Dholydai/writerz-with-an-attitude/KeycapSubs/Keycaps-for-single-hand-comp.jpg

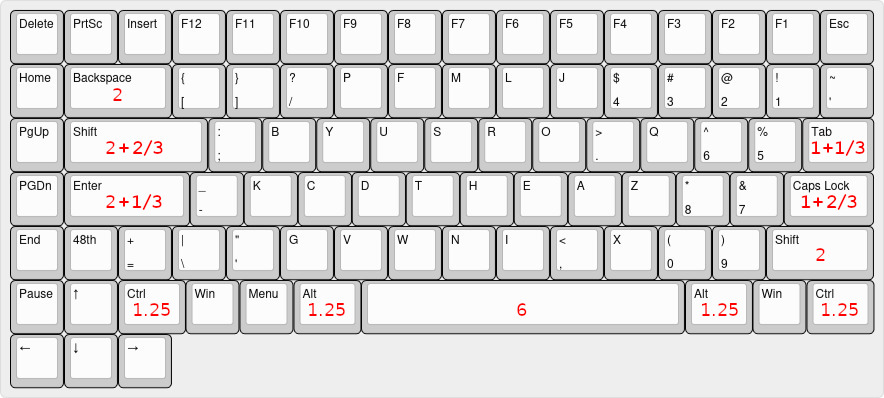
KeycapSubs/Keycaps-for-single-hand-comp.jpg
