Dholydai/writerz-with-an-attitude/KeycapSubs/Keycaps-for-two-hand-comp.png

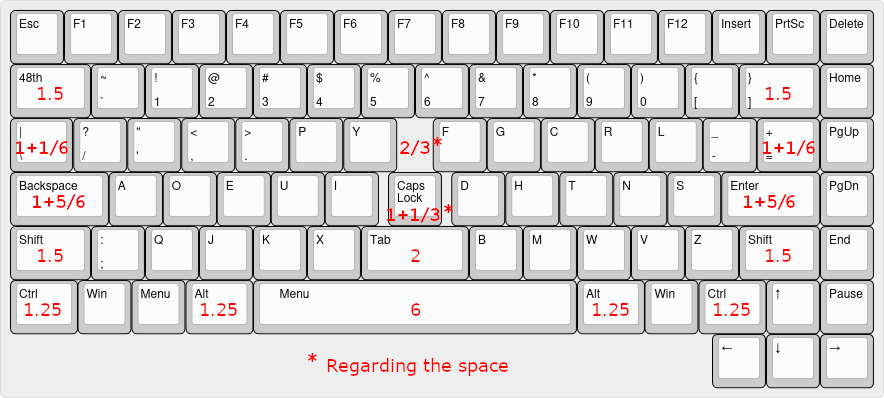
KeycapSubs/Keycaps-for-two-hand-comp.png
