Dholydai/writerz-with-an-attitude/KeycapSubs/Single-hand-keycap-subs.png

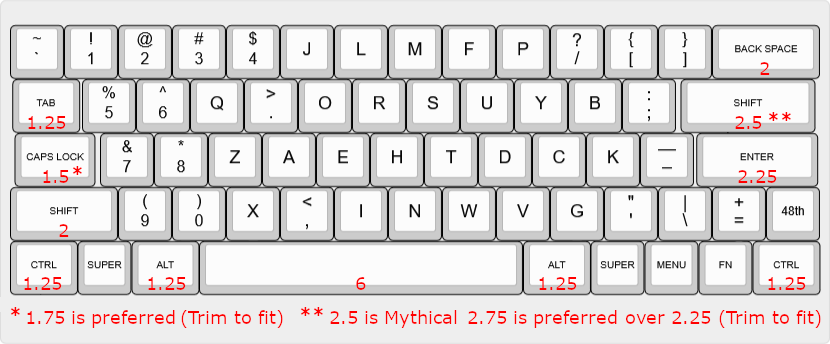
KeycapSubs/Single-hand-keycap-subs.png
