Dholydai/writerz-with-an-attitude/KeycapSubs/Two-hand-keycap-subs.png

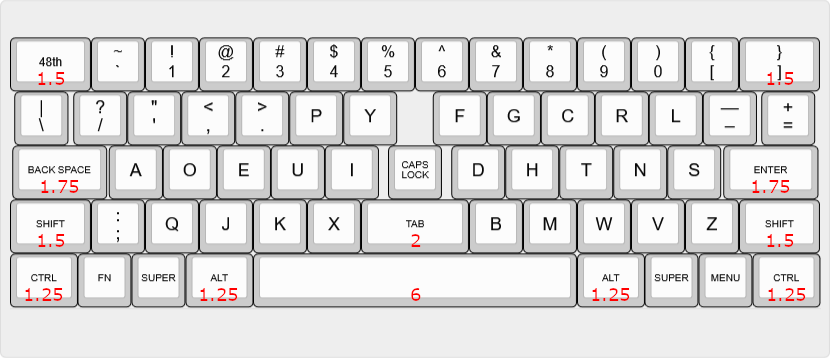
KeycapSubs/Two-hand-keycap-subs.png
