Dholydai/writerz-with-an-attitude/Layout/Dhlyd2Hnd60Lft.png

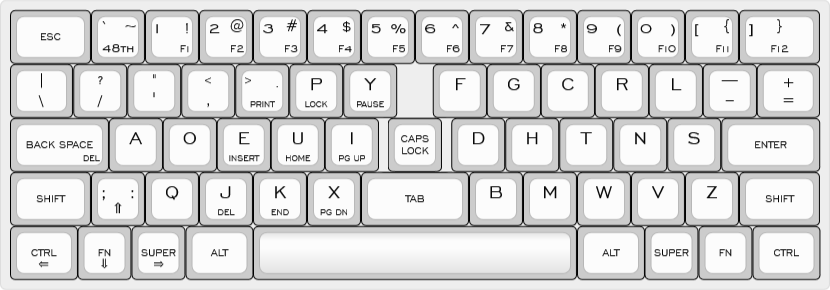
Layout/Dhlyd2Hnd60Lft.png
