Dholydai/writerz-with-an-attitude/Layout/Dhlyd2Hnd60Rgt.png

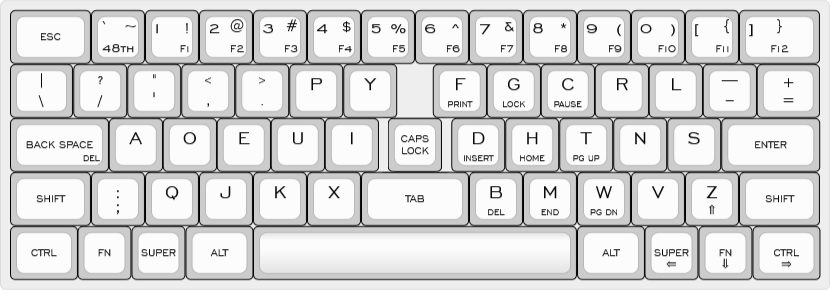
Layout/Dhlyd2Hnd60Rgt.png
