Dholydai/writerz-with-an-attitude/Layout/Dhlyd2HndCmp.png

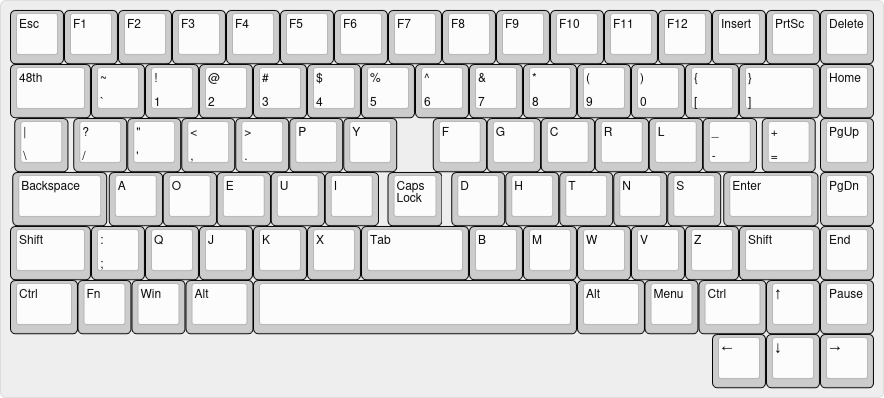
Layout/Dhlyd2HndCmp.png
