Dholydai/writerz-with-an-attitude/Layout/Dhlyd2HndMax.png

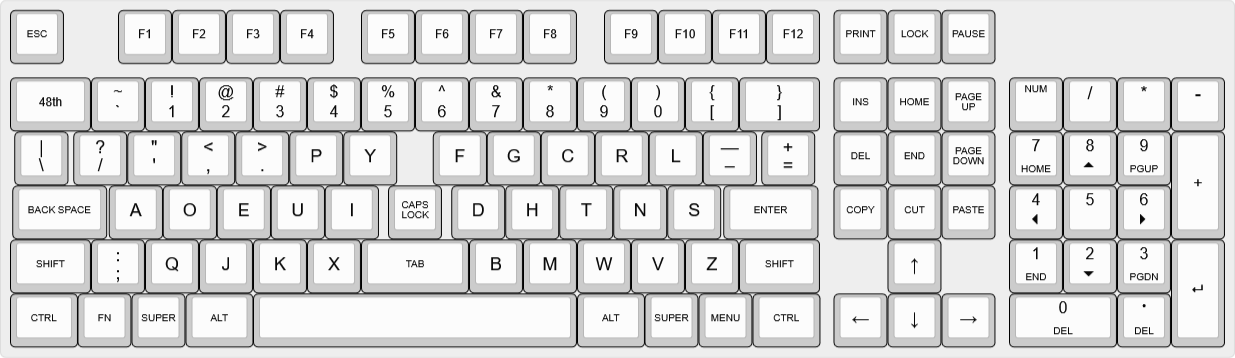
Layout/Dhlyd2HndMax.png
