Dholydai/writerz-with-an-attitude/Layout/DhlydLeftComp.png

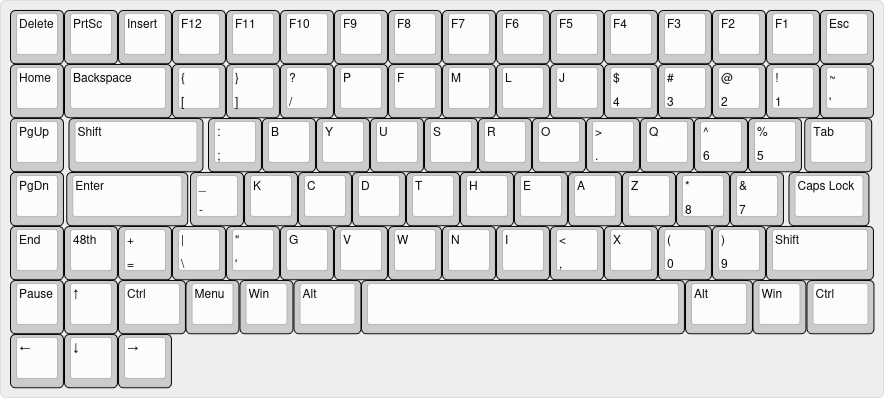
Layout/DhlydLeftComp.png
