Dholydai/writerz-with-an-attitude/Layout/DhlydRightComp.png

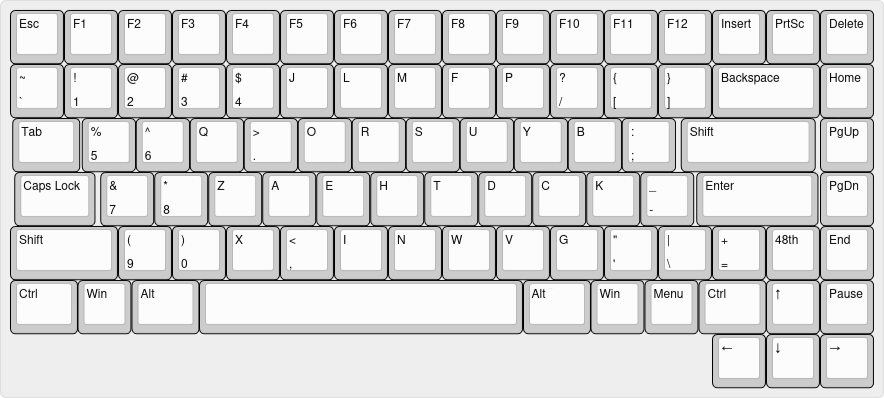
Layout/DhlydRightComp.png
