Dholydai/writerz-with-an-attitude/Matrix/Dhlyd2HndCmp.png

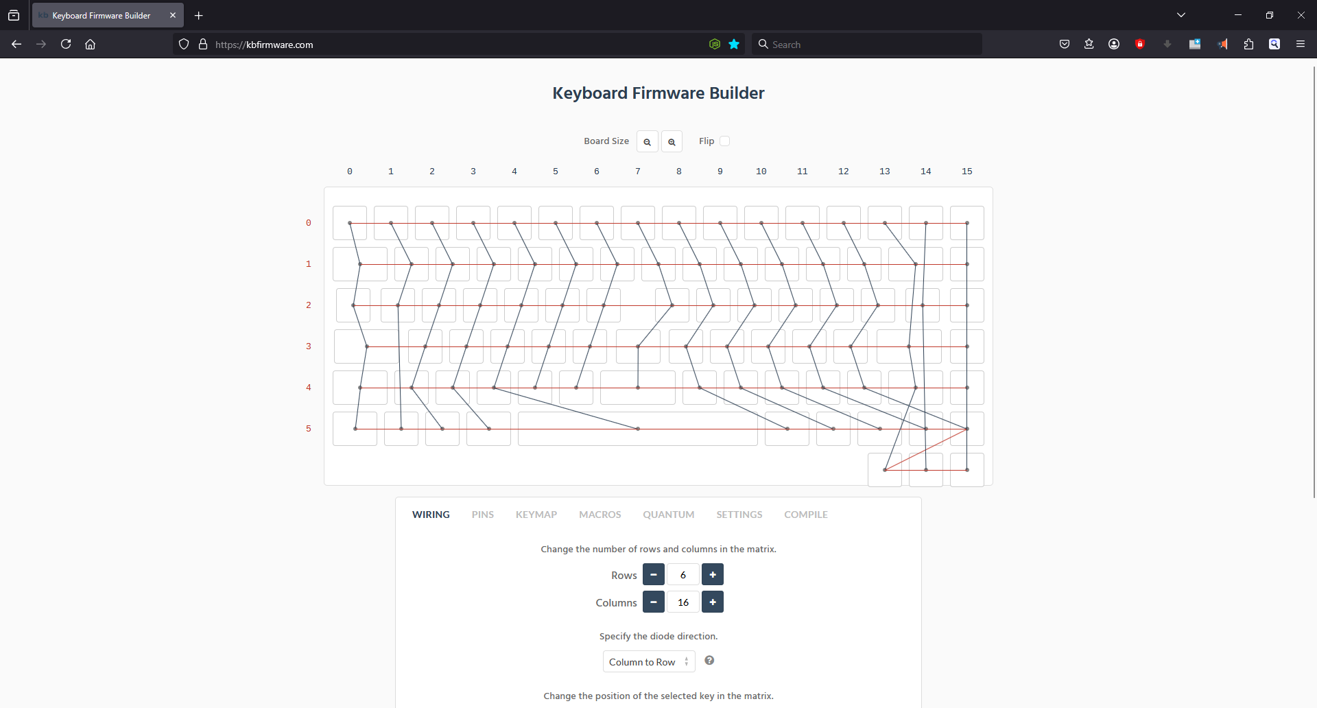
Matrix/Dhlyd2HndCmp.png
