Dholydai/writerz-with-an-attitude/Matrix/Dhlyd2HndMax.png

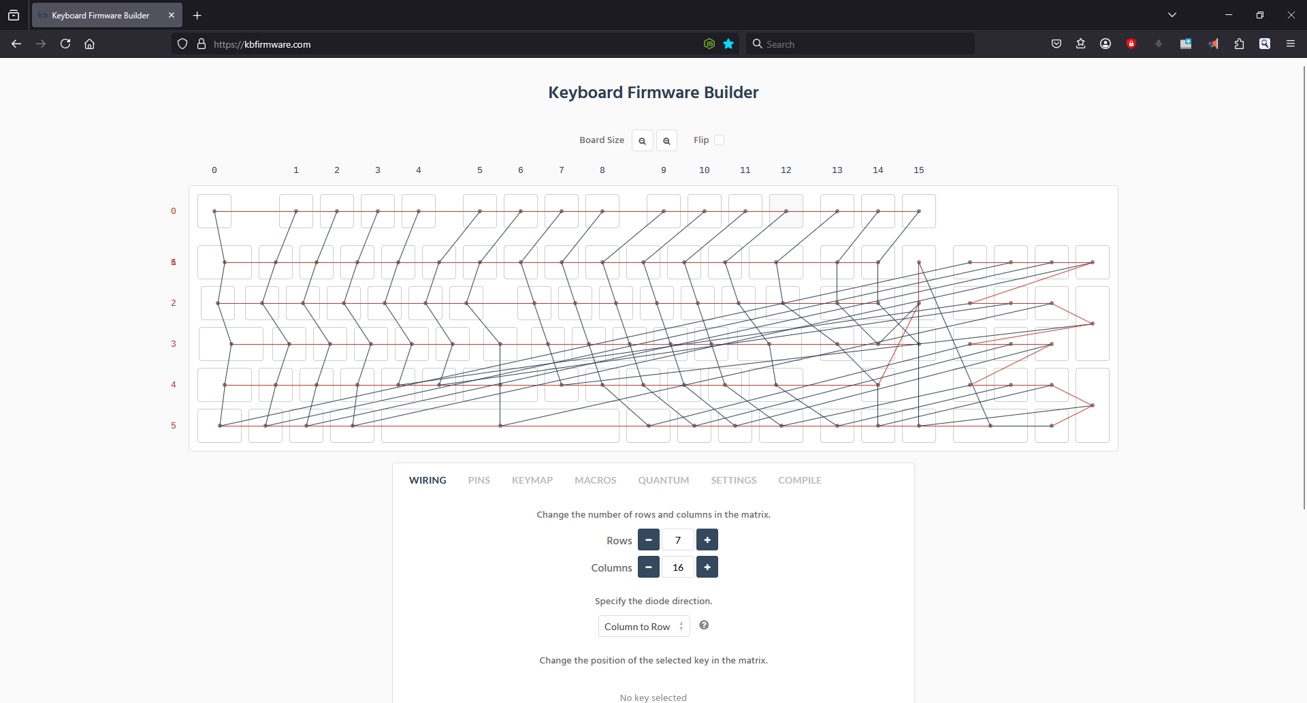
Matrix/Dhlyd2HndMax.png
