Dholydai/writerz-with-an-attitude/Matrix/DhlydLeftCmp.png

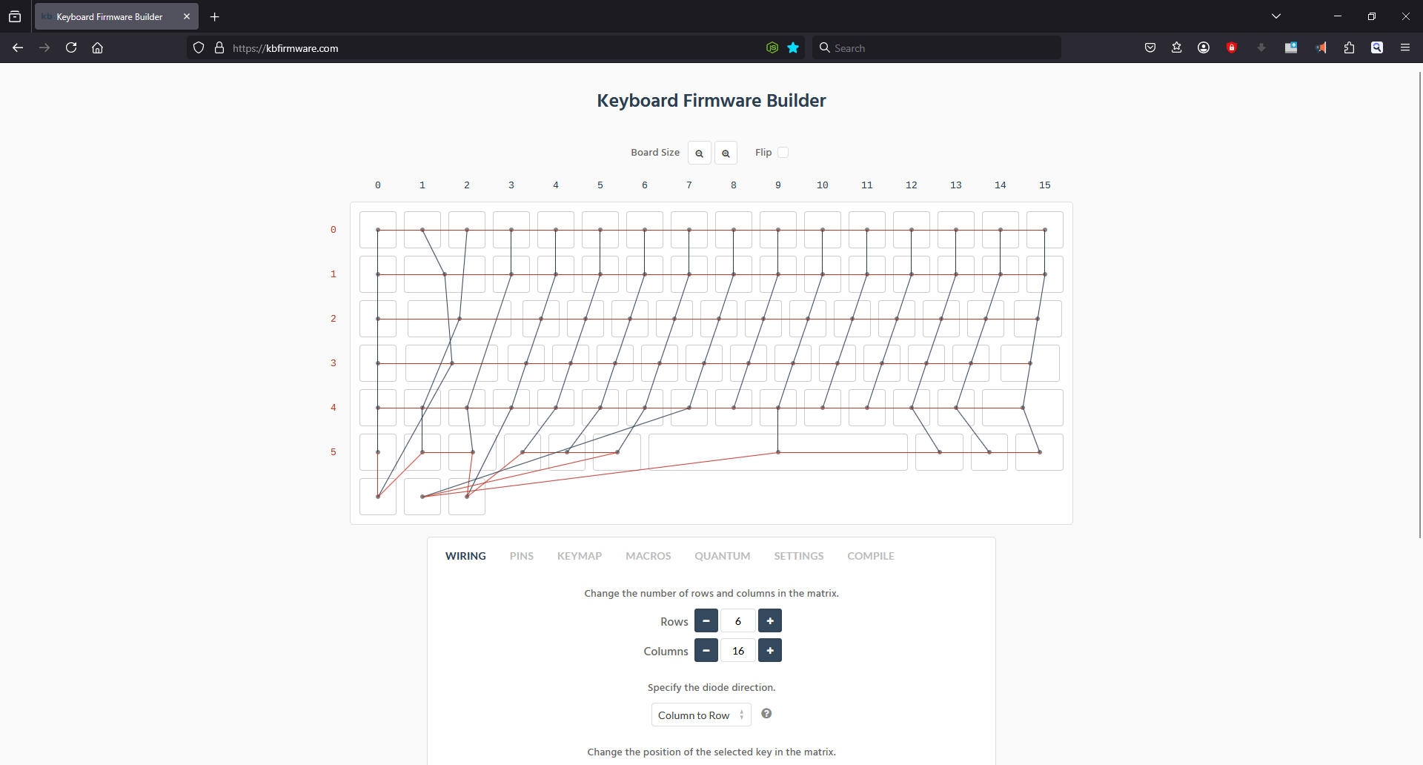
Matrix/DhlydLeftCmp.png
