Dholydai/writerz-with-an-attitude/Nuevo Universal/Brazil/BlkQX1-Brazil.png

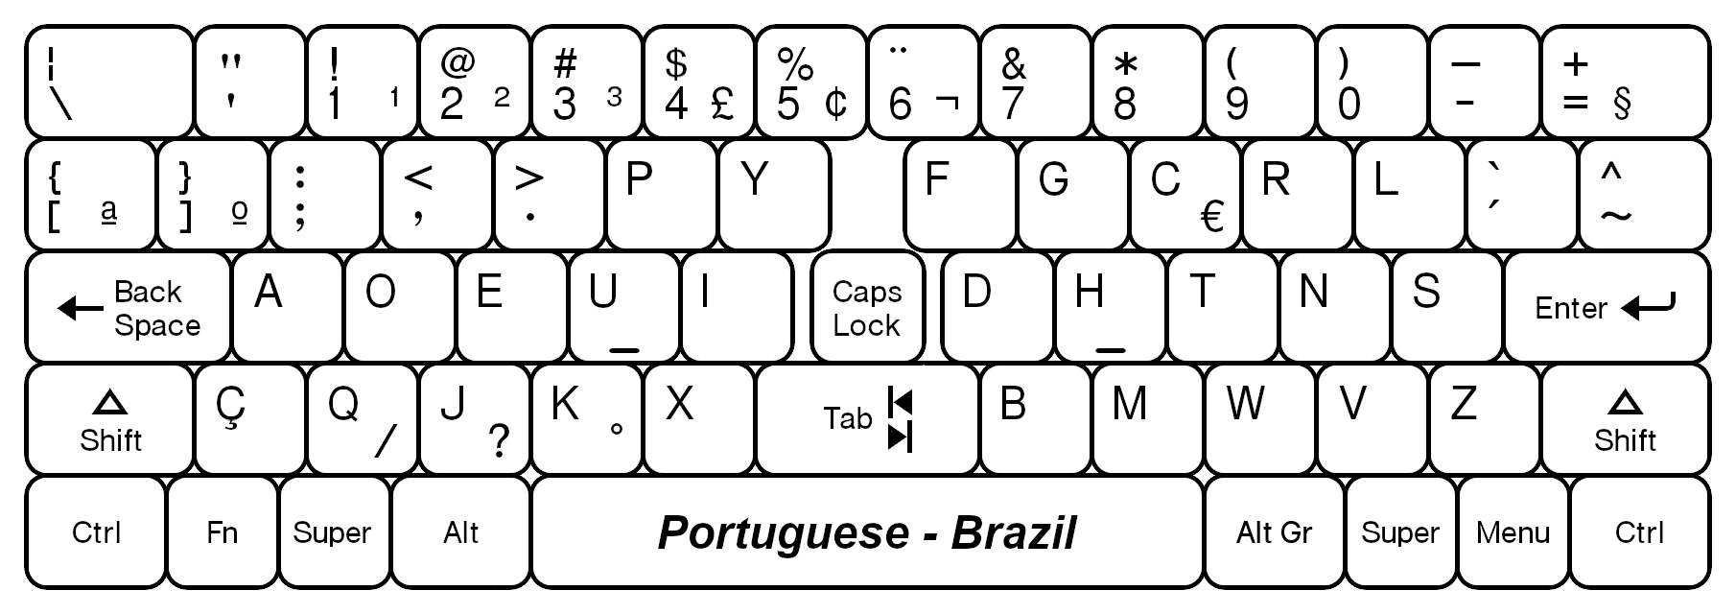
Nuevo Universal/Brazil/BlkQX1-Brazil.png
