Dholydai/writerz-with-an-attitude/Nuevo Universal/Czechia/BlkQX1-Czech.png

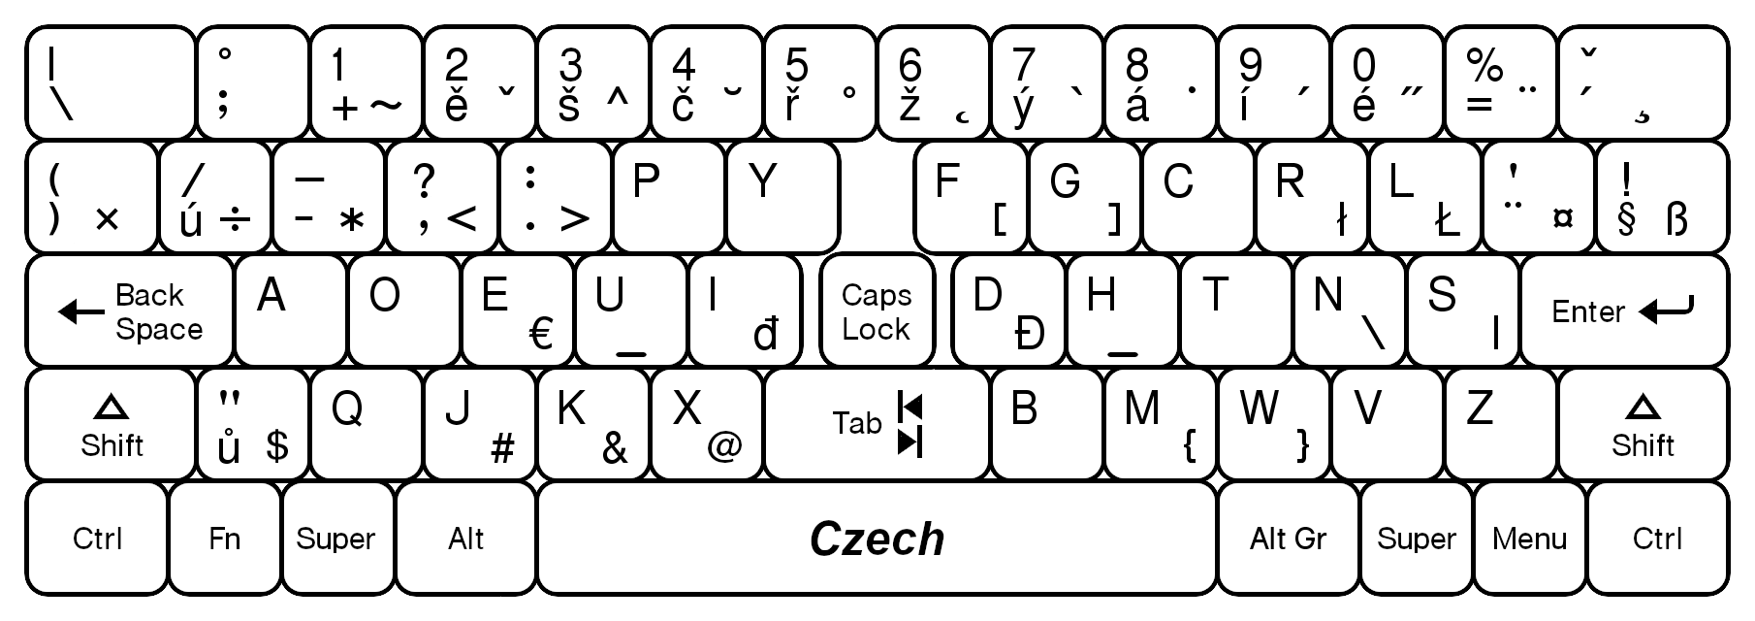
Nuevo Universal/Czechia/BlkQX1-Czech.png
