Dholydai/writerz-with-an-attitude/Nuevo Universal/Spain/BlkQX1-Spanish.png

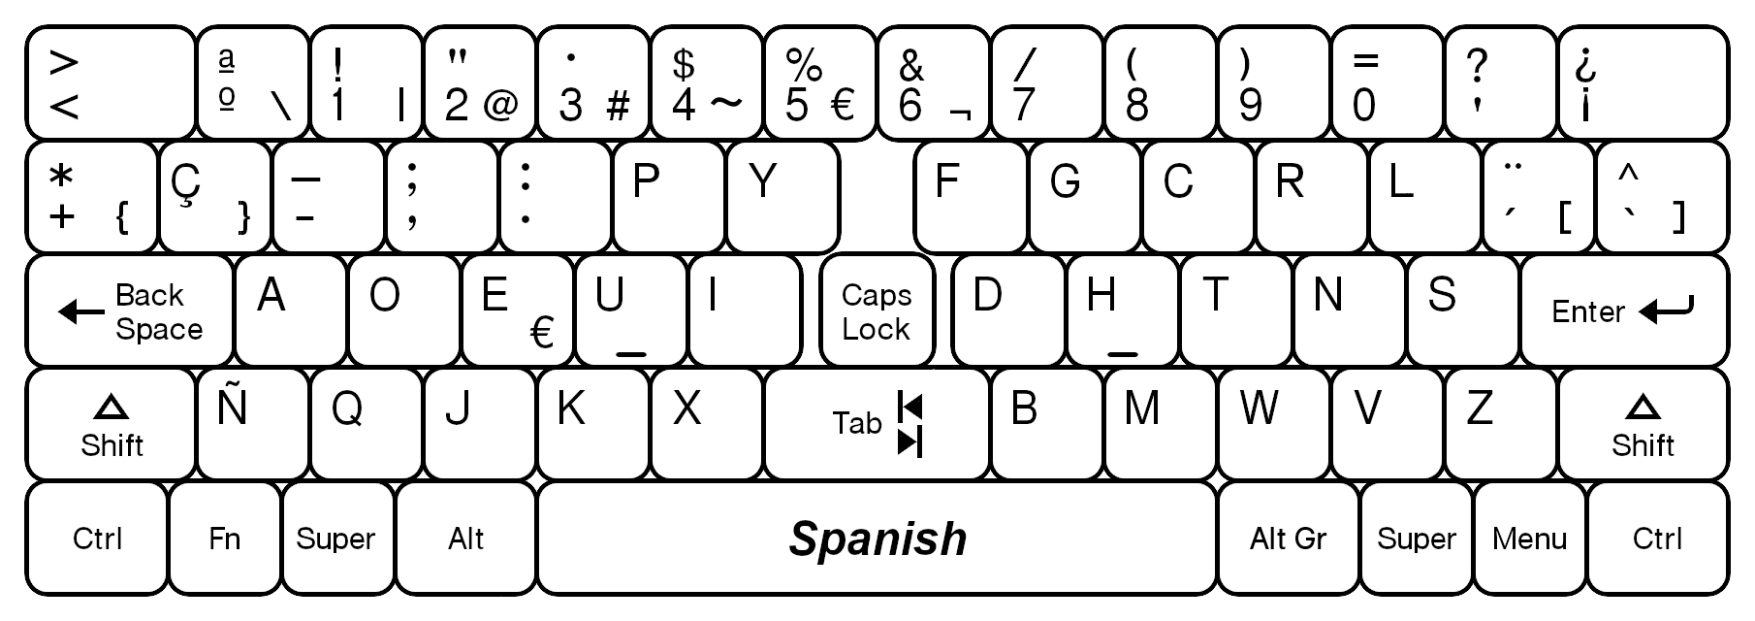
Nuevo Universal/Spain/BlkQX1-Spanish.png
