Dholydai/writerz-with-an-attitude/Dhlyd2HandMaximus/Case2HndMaximus/Stl/Max2HndBtmRgt.stl

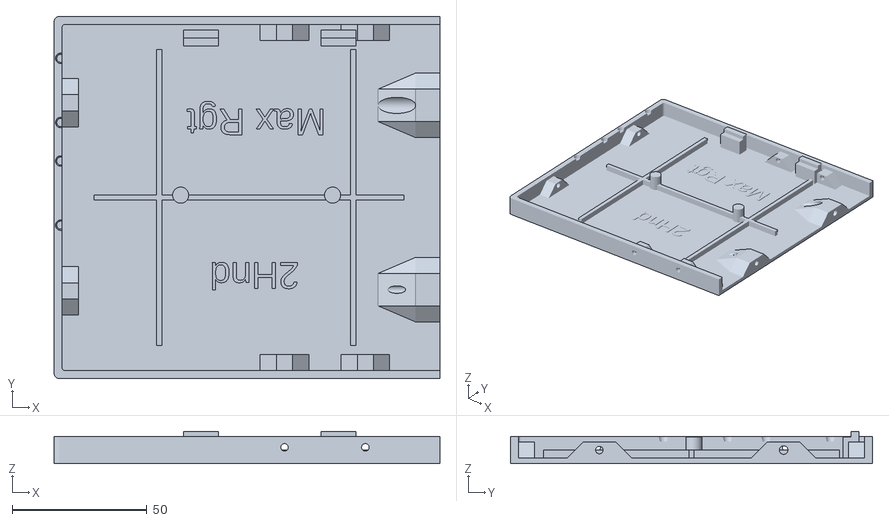
[picture p41: CAD file, 2026-07-24]
Dhlyd2HandMaximus/Case2HndMaximus/Stl/Max2HndBtmRgt.stl
143.2 x 134.3 x 11.9
