Dholydai/writerz-with-an-attitude/Dhlyd2HandCompact/Case2HndComp/Stl/Comp2HndTopRgt.stl

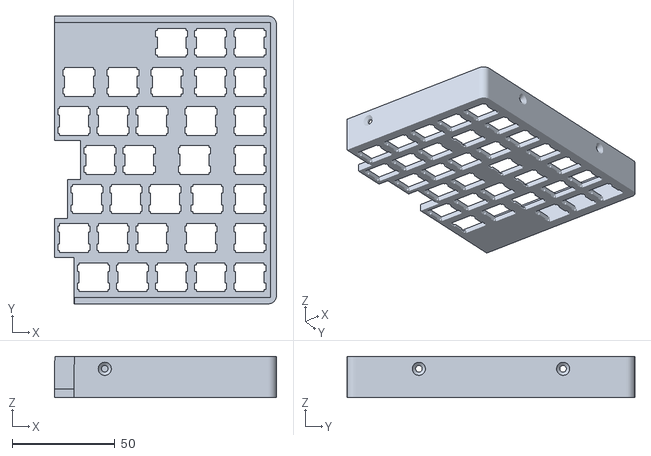
[picture p42: CAD file, 2026-07-24]
Dhlyd2HandCompact/Case2HndComp/Stl/Comp2HndTopRgt.stl
108.3 x 140.4 x 20.0
