Dholydai/writerz-with-an-attitude/DhlydRightCompact/CaseRightHndComp/Stl/CompRightTopRgt.stl

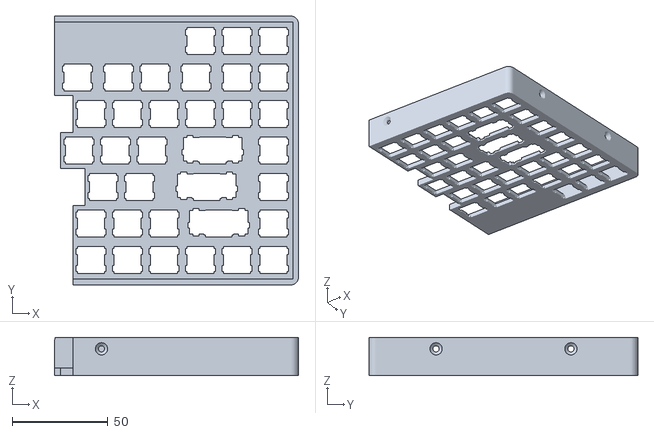
[picture p43: CAD file, 2026-07-24]
DhlydRightCompact/CaseRightHndComp/Stl/CompRightTopRgt.stl
127.3 x 140.4 x 20.0
