Dholydai/writerz-with-an-attitude/Dhlyd2Hand60Percent/Case2Hnd60Per/Stl/SixtyTopLft.stl

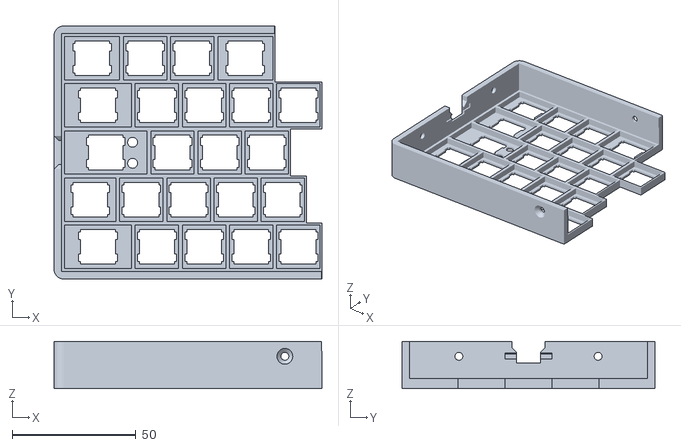
[picture p44: CAD file, 2026-07-24]
Dhlyd2Hand60Percent/Case2Hnd60Per/Stl/SixtyTopLft.stl
108.3 x 102.2 x 19.0
