Dholydai/writerz-with-an-attitude/Dhlyd2HandMaximus/Case2HndMaximus/Stl/Max2HndTopRgt.stl

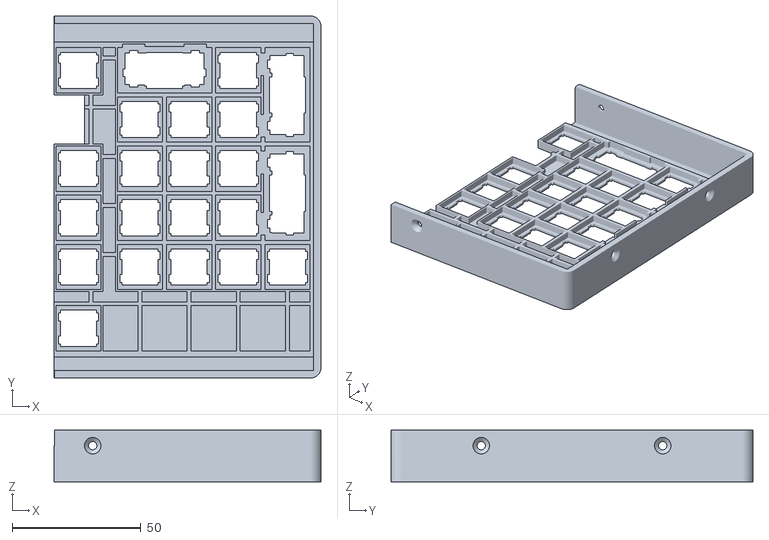
[picture p45: CAD file, 2026-07-24]
Dhlyd2HandMaximus/Case2HndMaximus/Stl/Max2HndTopRgt.stl
103.5 x 140.4 x 20.0
