Dholydai/writerz-with-an-attitude/Dhlyd2HandMaximus/Case2HndMaximus/Stl/Max2HndBtmMid.stl

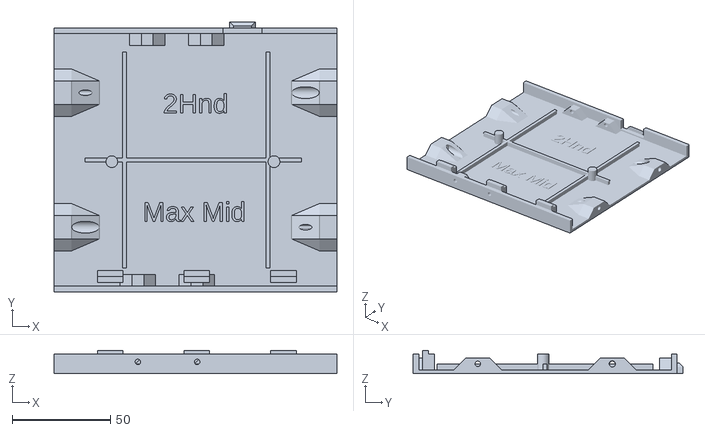
[picture p46: CAD file, 2026-07-24]
Dhlyd2HandMaximus/Case2HndMaximus/Stl/Max2HndBtmMid.stl
143.8 x 137.3 x 11.9
