Dholydai/writerz-with-an-attitude/Dhlyd2HandMaximus/Case2HndMaximus/Stl/Max2HndTopLft.stl

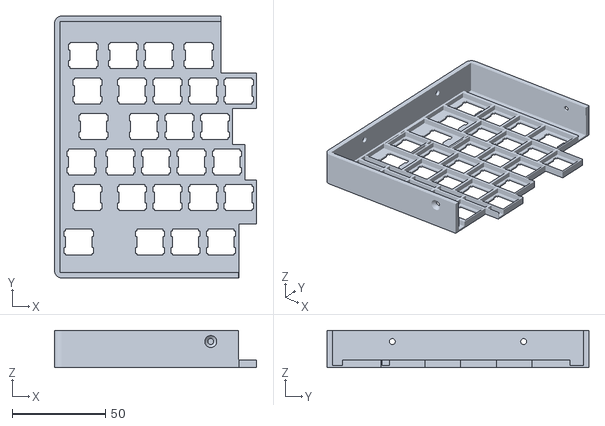
[picture p47: CAD file, 2026-07-24]
Dhlyd2HandMaximus/Case2HndMaximus/Stl/Max2HndTopLft.stl
108.3 x 140.4 x 20.0
