Dholydai/writerz-with-an-attitude/Dhlyd2Hand60Percent/Case2Hnd60Per/OpenSCAD/SixtyTopLft.scad

// Generated by SolidPython 1.1.3 on 2024-12-20 13:12:54
// Sixty has a 19mm sidewall for proportionality.
// Modified by Dholydai
// Add countersunk screw holes thru the sidewalls
// Add reset/run holes and USB port hole for U1.
// Add shallow angle cuts to the sidewall butt faces, compensating for printer artifacts.
// Change USB port wedges to truncated 10 Jul 2026


$fn = 32;

difference() {
  union () {
        difference() {
difference() {
	union() {
		translate(v = [0, 0, 18.4445000000]) {
			translate(v = [0, 98.7500000000, 0]) {
				translate(v = [3.5000000000, 0, 0]) {
					difference() {
						union() {
							difference() {
								union() {
									union() {
										translate(v = [142.8750000000, 0, 0]) {
											translate(v = [0, -47.6250000000, 0]) {
												minkowski() {
													cube(center = true, size = [284.7500000000, 94.2500000000, 0.5555000000]);
													cylinder(center = true, h = 0.5555000000, r = 4);
												}
											}
										}
										translate(v = [0, -95.2500000000, 0]) {
											translate(v = [0, 0, -3.5555000000]) {
												difference() {
													translate(v = [-1.5000000000, 0, 0]) {
														translate(v = [0, -1.5000000000, 0]) {
															cube(size = [288.7500000000, 98.2500000000, 4.1110000000]);
														}
													}
													cube(size = [285.7500000000, 95.2500000000, 3.0000000000]);
												}
											}
										}
										translate(v = [0.0000000000, 0, 0]) {
											translate(v = [0, 0.0000000000, 0]) {
												union() {
													translate(v = [9.5250000000, 0, 0]) {
														translate(v = [0, -9.5250000000, 0]) {
															cube(center = true, size = [19.0500000000, 19.0500000000, 1.1110000000]);
														}
													}
													translate(v = [9.5250000000, 0, 0]) {
														translate(v = [0, -9.5250000000, 0]) {
															difference() {
																translate(v = [0, 0, -1.5000000000]) {
																	cube(center = true, size = [19.0500000000, 19.0500000000, 4.1110000000]);
																}
																translate(v = [0, 0, -1.5000000000]) {
																	cube(center = true, size = [17.5500000000, 17.5500000000, 6.0000000000]);
																}
															}
														}
													}
												}
											}
										}
										translate(v = [0.0000000000, 0, 0]) {
											translate(v = [0, -19.0500000000, 0]) {
												union() {
													translate(v = [9.5250000000, 0, 0]) {
														translate(v = [0, -9.5250000000, 0]) {
															cube(center = true, size = [19.0500000000, 19.0500000000, 1.1110000000]);
														}
													}
													translate(v = [9.5250000000, 0, 0]) {
														translate(v = [0, -9.5250000000, 0]) {
															difference() {
																translate(v = [0, 0, -1.5000000000]) {
																	cube(center = true, size = [19.0500000000, 19.0500000000, 4.1110000000]);
																}
																translate(v = [0, 0, -1.5000000000]) {
																	cube(center = true, size = [17.5500000000, 17.5500000000, 6.0000000000]);
																}
															}
														}
													}
												}
											}
										}
										translate(v = [0.0000000000, 0, 0]) {
											translate(v = [0, -38.1000000000, 0]) {
												union() {
													translate(v = [9.5250000000, 0, 0]) {
														translate(v = [0, -9.5250000000, 0]) {
															cube(center = true, size = [19.0500000000, 19.0500000000, 1.1110000000]);
														}
													}
													translate(v = [9.5250000000, 0, 0]) {
														translate(v = [0, -9.5250000000, 0]) {
															difference() {
																translate(v = [0, 0, -1.5000000000]) {
																	cube(center = true, size = [19.0500000000, 19.0500000000, 4.1110000000]);
																}
																translate(v = [0, 0, -1.5000000000]) {
																	cube(center = true, size = [17.5500000000, 17.5500000000, 6.0000000000]);
																}
															}
														}
													}
												}
											}
										}
										translate(v = [0.0000000000, 0, 0]) {
											translate(v = [0, -57.1500000000, 0]) {
												union() {
													translate(v = [9.5250000000, 0, 0]) {
														translate(v = [0, -9.5250000000, 0]) {
															cube(center = true, size = [19.0500000000, 19.0500000000, 1.1110000000]);
														}
													}
													translate(v = [9.5250000000, 0, 0]) {
														translate(v = [0, -9.5250000000, 0]) {
															difference() {
																translate(v = [0, 0, -1.5000000000]) {
																	cube(center = true, size = [19.0500000000, 19.0500000000, 4.1110000000]);
																}
																translate(v = [0, 0, -1.5000000000]) {
																	cube(center = true, size = [17.5500000000, 17.5500000000, 6.0000000000]);
																}
															}
														}
													}
												}
											}
										}
										translate(v = [0.0000000000, 0, 0]) {
											translate(v = [0, -76.2000000000, 0]) {
												union() {
													translate(v = [9.5250000000, 0, 0]) {
														translate(v = [0, -9.5250000000, 0]) {
															cube(center = true, size = [19.0500000000, 19.0500000000, 1.1110000000]);
														}
													}
													translate(v = [9.5250000000, 0, 0]) {
														translate(v = [0, -9.5250000000, 0]) {
															difference() {
																translate(v = [0, 0, -1.5000000000]) {
																	cube(center = true, size = [19.0500000000, 19.0500000000, 4.1110000000]);
																}
																translate(v = [0, 0, -1.5000000000]) {
																	cube(center = true, size = [17.5500000000, 17.5500000000, 6.0000000000]);
																}
															}
														}
													}
												}
											}
										}
										translate(v = [19.0500000000, 0, 0]) {
											translate(v = [0, 0.0000000000, 0]) {
												union() {
													translate(v = [9.5250000000, 0, 0]) {
														translate(v = [0, -9.5250000000, 0]) {
															cube(center = true, size = [19.0500000000, 19.0500000000, 1.1110000000]);
														}
													}
													translate(v = [9.5250000000, 0, 0]) {
														translate(v = [0, -9.5250000000, 0]) {
															difference() {
																translate(v = [0, 0, -1.5000000000]) {
																	cube(center = true, size = [19.0500000000, 19.0500000000, 4.1110000000]);
																}
																translate(v = [0, 0, -1.5000000000]) {
																	cube(center = true, size = [17.5500000000, 17.5500000000, 6.0000000000]);
																}
															}
														}
													}
												}
											}
										}
										translate(v = [19.0500000000, 0, 0]) {
											translate(v = [0, -19.0500000000, 0]) {
												union() {
													translate(v = [9.5250000000, 0, 0]) {
														translate(v = [0, -9.5250000000, 0]) {
															cube(center = true, size = [19.0500000000, 19.0500000000, 1.1110000000]);
														}
													}
													translate(v = [9.5250000000, 0, 0]) {
														translate(v = [0, -9.5250000000, 0]) {
															difference() {
																translate(v = [0, 0, -1.5000000000]) {
																	cube(center = true, size = [19.0500000000, 19.0500000000, 4.1110000000]);
																}
																translate(v = [0, 0, -1.5000000000]) {
																	cube(center = true, size = [17.5500000000, 17.5500000000, 6.0000000000]);
																}
															}
														}
													}
												}
											}
										}
										translate(v = [19.0500000000, 0, 0]) {
											translate(v = [0, -38.1000000000, 0]) {
												union() {
													translate(v = [9.5250000000, 0, 0]) {
														translate(v = [0, -9.5250000000, 0]) {
															cube(center = true, size = [19.0500000000, 19.0500000000, 1.1110000000]);
														}
													}
													translate(v = [9.5250000000, 0, 0]) {
														translate(v = [0, -9.5250000000, 0]) {
															difference() {
																translate(v = [0, 0, -1.5000000000]) {
																	cube(center = true, size = [19.0500000000, 19.0500000000, 4.1110000000]);
																}
																translate(v = [0, 0, -1.5000000000]) {
																	cube(center = true, size = [17.5500000000, 17.5500000000, 6.0000000000]);
																}
															}
														}
													}
												}
											}
										}
										translate(v = [19.0500000000, 0, 0]) {
											translate(v = [0, -57.1500000000, 0]) {
												union() {
													translate(v = [9.5250000000, 0, 0]) {
														translate(v = [0, -9.5250000000, 0]) {
															cube(center = true, size = [19.0500000000, 19.0500000000, 1.1110000000]);
														}
													}
													translate(v = [9.5250000000, 0, 0]) {
														translate(v = [0, -9.5250000000, 0]) {
															difference() {
																translate(v = [0, 0, -1.5000000000]) {
																	cube(center = true, size = [19.0500000000, 19.0500000000, 4.1110000000]);
																}
																translate(v = [0, 0, -1.5000000000]) {
																	cube(center = true, size = [17.5500000000, 17.5500000000, 6.0000000000]);
																}
															}
														}
													}
												}
											}
										}
										translate(v = [19.0500000000, 0, 0]) {
											translate(v = [0, -76.2000000000, 0]) {
												union() {
													translate(v = [9.5250000000, 0, 0]) {
														translate(v = [0, -9.5250000000, 0]) {
															cube(center = true, size = [19.0500000000, 19.0500000000, 1.1110000000]);
														}
													}
													translate(v = [9.5250000000, 0, 0]) {
														translate(v = [0, -9.5250000000, 0]) {
															difference() {
																translate(v = [0, 0, -1.5000000000]) {
																	cube(center = true, size = [19.0500000000, 19.0500000000, 4.1110000000]);
																}
																translate(v = [0, 0, -1.5000000000]) {
																	cube(center = true, size = [17.5500000000, 17.5500000000, 6.0000000000]);
																}
															}
														}
													}
												}
											}
										}
										translate(v = [38.1000000000, 0, 0]) {
											translate(v = [0, 0.0000000000, 0]) {
												union() {
													translate(v = [9.5250000000, 0, 0]) {
														translate(v = [0, -9.5250000000, 0]) {
															cube(center = true, size = [19.0500000000, 19.0500000000, 1.1110000000]);
														}
													}
													translate(v = [9.5250000000, 0, 0]) {
														translate(v = [0, -9.5250000000, 0]) {
															difference() {
																translate(v = [0, 0, -1.5000000000]) {
																	cube(center = true, size = [19.0500000000, 19.0500000000, 4.1110000000]);
																}
																translate(v = [0, 0, -1.5000000000]) {
																	cube(center = true, size = [17.5500000000, 17.5500000000, 6.0000000000]);
																}
															}
														}
													}
												}
											}
										}
										translate(v = [38.1000000000, 0, 0]) {
											translate(v = [0, -19.0500000000, 0]) {
												union() {
													translate(v = [9.5250000000, 0, 0]) {
														translate(v = [0, -9.5250000000, 0]) {
															cube(center = true, size = [19.0500000000, 19.0500000000, 1.1110000000]);
														}
													}
													translate(v = [9.5250000000, 0, 0]) {
														translate(v = [0, -9.5250000000, 0]) {
															difference() {
																translate(v = [0, 0, -1.5000000000]) {
																	cube(center = true, size = [19.0500000000, 19.0500000000, 4.1110000000]);
																}
																translate(v = [0, 0, -1.5000000000]) {
																	cube(center = true, size = [17.5500000000, 17.5500000000, 6.0000000000]);
																}
															}
														}
													}
												}
											}
										}
										translate(v = [38.1000000000, 0, 0]) {
											translate(v = [0, -38.1000000000, 0]) {
												union() {
													translate(v = [9.5250000000, 0, 0]) {
														translate(v = [0, -9.5250000000, 0]) {
															cube(center = true, size = [19.0500000000, 19.0500000000, 1.1110000000]);
														}
													}
													translate(v = [9.5250000000, 0, 0]) {
														translate(v = [0, -9.5250000000, 0]) {
															difference() {
																translate(v = [0, 0, -1.5000000000]) {
																	cube(center = true, size = [19.0500000000, 19.0500000000, 4.1110000000]);
																}
																translate(v = [0, 0, -1.5000000000]) {
																	cube(center = true, size = [17.5500000000, 17.5500000000, 6.0000000000]);
																}
															}
														}
													}
												}
											}
										}
										translate(v = [38.1000000000, 0, 0]) {
											translate(v = [0, -57.1500000000, 0]) {
												union() {
													translate(v = [9.5250000000, 0, 0]) {
														translate(v = [0, -9.5250000000, 0]) {
															cube(center = true, size = [19.0500000000, 19.0500000000, 1.1110000000]);
														}
													}
													translate(v = [9.5250000000, 0, 0]) {
														translate(v = [0, -9.5250000000, 0]) {
															difference() {
																translate(v = [0, 0, -1.5000000000]) {
																	cube(center = true, size = [19.0500000000, 19.0500000000, 4.1110000000]);
																}
																translate(v = [0, 0, -1.5000000000]) {
																	cube(center = true, size = [17.5500000000, 17.5500000000, 6.0000000000]);
																}
															}
														}
													}
												}
											}
										}
										translate(v = [38.1000000000, 0, 0]) {
											translate(v = [0, -76.2000000000, 0]) {
												union() {
													translate(v = [9.5250000000, 0, 0]) {
														translate(v = [0, -9.5250000000, 0]) {
															cube(center = true, size = [19.0500000000, 19.0500000000, 1.1110000000]);
														}
													}
													translate(v = [9.5250000000, 0, 0]) {
														translate(v = [0, -9.5250000000, 0]) {
															difference() {
																translate(v = [0, 0, -1.5000000000]) {
																	cube(center = true, size = [19.0500000000, 19.0500000000, 4.1110000000]);
																}
																translate(v = [0, 0, -1.5000000000]) {
																	cube(center = true, size = [17.5500000000, 17.5500000000, 6.0000000000]);
																}
															}
														}
													}
												}
											}
										}
										translate(v = [57.1500000000, 0, 0]) {
											translate(v = [0, 0.0000000000, 0]) {
												union() {
													translate(v = [9.5250000000, 0, 0]) {
														translate(v = [0, -9.5250000000, 0]) {
															cube(center = true, size = [19.0500000000, 19.0500000000, 1.1110000000]);
														}
													}
													translate(v = [9.5250000000, 0, 0]) {
														translate(v = [0, -9.5250000000, 0]) {
															difference() {
																translate(v = [0, 0, -1.5000000000]) {
																	cube(center = true, size = [19.0500000000, 19.0500000000, 4.1110000000]);
																}
																translate(v = [0, 0, -1.5000000000]) {
																	cube(center = true, size = [17.5500000000, 17.5500000000, 6.0000000000]);
																}
															}
														}
													}
												}
											}
										}
										translate(v = [57.1500000000, 0, 0]) {
											translate(v = [0, -19.0500000000, 0]) {
												union() {
													translate(v = [9.5250000000, 0, 0]) {
														translate(v = [0, -9.5250000000, 0]) {
															cube(center = true, size = [19.0500000000, 19.0500000000, 1.1110000000]);
														}
													}
													translate(v = [9.5250000000, 0, 0]) {
														translate(v = [0, -9.5250000000, 0]) {
															difference() {
																translate(v = [0, 0, -1.5000000000]) {
																	cube(center = true, size = [19.0500000000, 19.0500000000, 4.1110000000]);
																}
																translate(v = [0, 0, -1.5000000000]) {
																	cube(center = true, size = [17.5500000000, 17.5500000000, 6.0000000000]);
																}
															}
														}
													}
												}
											}
										}
										translate(v = [57.1500000000, 0, 0]) {
											translate(v = [0, -38.1000000000, 0]) {
												union() {
													translate(v = [9.5250000000, 0, 0]) {
														translate(v = [0, -9.5250000000, 0]) {
															cube(center = true, size = [19.0500000000, 19.0500000000, 1.1110000000]);
														}
													}
													translate(v = [9.5250000000, 0, 0]) {
														translate(v = [0, -9.5250000000, 0]) {
															difference() {
																translate(v = [0, 0, -1.5000000000]) {
																	cube(center = true, size = [19.0500000000, 19.0500000000, 4.1110000000]);
																}
																translate(v = [0, 0, -1.5000000000]) {
																	cube(center = true, size = [17.5500000000, 17.5500000000, 6.0000000000]);
																}
															}
														}
													}
												}
											}
										}
										translate(v = [57.1500000000, 0, 0]) {
											translate(v = [0, -57.1500000000, 0]) {
												union() {
													translate(v = [9.5250000000, 0, 0]) {
														translate(v = [0, -9.5250000000, 0]) {
															cube(center = true, size = [19.0500000000, 19.0500000000, 1.1110000000]);
														}
													}
													translate(v = [9.5250000000, 0, 0]) {
														translate(v = [0, -9.5250000000, 0]) {
															difference() {
																translate(v = [0, 0, -1.5000000000]) {
																	cube(center = true, size = [19.0500000000, 19.0500000000, 4.1110000000]);
																}
																translate(v = [0, 0, -1.5000000000]) {
																	cube(center = true, size = [17.5500000000, 17.5500000000, 6.0000000000]);
																}
															}
														}
													}
												}
											}
										}
										translate(v = [57.1500000000, 0, 0]) {
											translate(v = [0, -76.2000000000, 0]) {
												union() {
													translate(v = [9.5250000000, 0, 0]) {
														translate(v = [0, -9.5250000000, 0]) {
															cube(center = true, size = [19.0500000000, 19.0500000000, 1.1110000000]);
														}
													}
													translate(v = [9.5250000000, 0, 0]) {
														translate(v = [0, -9.5250000000, 0]) {
															difference() {
																translate(v = [0, 0, -1.5000000000]) {
																	cube(center = true, size = [19.0500000000, 19.0500000000, 4.1110000000]);
																}
																translate(v = [0, 0, -1.5000000000]) {
																	cube(center = true, size = [17.5500000000, 17.5500000000, 6.0000000000]);
																}
															}
														}
													}
												}
											}
										}
										translate(v = [76.2000000000, 0, 0]) {
											translate(v = [0, 0.0000000000, 0]) {
												union() {
													translate(v = [9.5250000000, 0, 0]) {
														translate(v = [0, -9.5250000000, 0]) {
															cube(center = true, size = [19.0500000000, 19.0500000000, 1.1110000000]);
														}
													}
													translate(v = [9.5250000000, 0, 0]) {
														translate(v = [0, -9.5250000000, 0]) {
															difference() {
																translate(v = [0, 0, -1.5000000000]) {
																	cube(center = true, size = [19.0500000000, 19.0500000000, 4.1110000000]);
																}
																translate(v = [0, 0, -1.5000000000]) {
																	cube(center = true, size = [17.5500000000, 17.5500000000, 6.0000000000]);
																}
															}
														}
													}
												}
											}
										}
										translate(v = [76.2000000000, 0, 0]) {
											translate(v = [0, -19.0500000000, 0]) {
												union() {
													translate(v = [9.5250000000, 0, 0]) {
														translate(v = [0, -9.5250000000, 0]) {
															cube(center = true, size = [19.0500000000, 19.0500000000, 1.1110000000]);
														}
													}
													translate(v = [9.5250000000, 0, 0]) {
														translate(v = [0, -9.5250000000, 0]) {
															difference() {
																translate(v = [0, 0, -1.5000000000]) {
																	cube(center = true, size = [19.0500000000, 19.0500000000, 4.1110000000]);
																}
																translate(v = [0, 0, -1.5000000000]) {
																	cube(center = true, size = [17.5500000000, 17.5500000000, 6.0000000000]);
																}
															}
														}
													}
												}
											}
										}
										translate(v = [76.2000000000, 0, 0]) {
											translate(v = [0, -38.1000000000, 0]) {
												union() {
													translate(v = [9.5250000000, 0, 0]) {
														translate(v = [0, -9.5250000000, 0]) {
															cube(center = true, size = [19.0500000000, 19.0500000000, 1.1110000000]);
														}
													}
													translate(v = [9.5250000000, 0, 0]) {
														translate(v = [0, -9.5250000000, 0]) {
															difference() {
																translate(v = [0, 0, -1.5000000000]) {
																	cube(center = true, size = [19.0500000000, 19.0500000000, 4.1110000000]);
																}
																translate(v = [0, 0, -1.5000000000]) {
																	cube(center = true, size = [17.5500000000, 17.5500000000, 6.0000000000]);
																}
															}
														}
													}
												}
											}
										}
										translate(v = [76.2000000000, 0, 0]) {
											translate(v = [0, -57.1500000000, 0]) {
												union() {
													translate(v = [9.5250000000, 0, 0]) {
														translate(v = [0, -9.5250000000, 0]) {
															cube(center = true, size = [19.0500000000, 19.0500000000, 1.1110000000]);
														}
													}
													translate(v = [9.5250000000, 0, 0]) {
														translate(v = [0, -9.5250000000, 0]) {
															difference() {
																translate(v = [0, 0, -1.5000000000]) {
																	cube(center = true, size = [19.0500000000, 19.0500000000, 4.1110000000]);
																}
																translate(v = [0, 0, -1.5000000000]) {
																	cube(center = true, size = [17.5500000000, 17.5500000000, 6.0000000000]);
																}
															}
														}
													}
												}
											}
										}
										translate(v = [76.2000000000, 0, 0]) {
											translate(v = [0, -76.2000000000, 0]) {
												union() {
													translate(v = [9.5250000000, 0, 0]) {
														translate(v = [0, -9.5250000000, 0]) {
															cube(center = true, size = [19.0500000000, 19.0500000000, 1.1110000000]);
														}
													}
													translate(v = [9.5250000000, 0, 0]) {
														translate(v = [0, -9.5250000000, 0]) {
															difference() {
																translate(v = [0, 0, -1.5000000000]) {
																	cube(center = true, size = [19.0500000000, 19.0500000000, 4.1110000000]);
																}
																translate(v = [0, 0, -1.5000000000]) {
																	cube(center = true, size = [17.5500000000, 17.5500000000, 6.0000000000]);
																}
															}
														}
													}
												}
											}
										}
										translate(v = [95.2500000000, 0, 0]) {
											translate(v = [0, 0.0000000000, 0]) {
												union() {
													translate(v = [9.5250000000, 0, 0]) {
														translate(v = [0, -9.5250000000, 0]) {
															cube(center = true, size = [19.0500000000, 19.0500000000, 1.1110000000]);
														}
													}
													translate(v = [9.5250000000, 0, 0]) {
														translate(v = [0, -9.5250000000, 0]) {
															difference() {
																translate(v = [0, 0, -1.5000000000]) {
																	cube(center = true, size = [19.0500000000, 19.0500000000, 4.1110000000]);
																}
																translate(v = [0, 0, -1.5000000000]) {
																	cube(center = true, size = [17.5500000000, 17.5500000000, 6.0000000000]);
																}
															}
														}
													}
												}
											}
										}
										translate(v = [95.2500000000, 0, 0]) {
											translate(v = [0, -19.0500000000, 0]) {
												union() {
													translate(v = [9.5250000000, 0, 0]) {
														translate(v = [0, -9.5250000000, 0]) {
															cube(center = true, size = [19.0500000000, 19.0500000000, 1.1110000000]);
														}
													}
													translate(v = [9.5250000000, 0, 0]) {
														translate(v = [0, -9.5250000000, 0]) {
															difference() {
																translate(v = [0, 0, -1.5000000000]) {
																	cube(center = true, size = [19.0500000000, 19.0500000000, 4.1110000000]);
																}
																translate(v = [0, 0, -1.5000000000]) {
																	cube(center = true, size = [17.5500000000, 17.5500000000, 6.0000000000]);
																}
															}
														}
													}
												}
											}
										}
										translate(v = [95.2500000000, 0, 0]) {
											translate(v = [0, -38.1000000000, 0]) {
												union() {
													translate(v = [9.5250000000, 0, 0]) {
														translate(v = [0, -9.5250000000, 0]) {
															cube(center = true, size = [19.0500000000, 19.0500000000, 1.1110000000]);
														}
													}
													translate(v = [9.5250000000, 0, 0]) {
														translate(v = [0, -9.5250000000, 0]) {
															difference() {
																translate(v = [0, 0, -1.5000000000]) {
																	cube(center = true, size = [19.0500000000, 19.0500000000, 4.1110000000]);
																}
																translate(v = [0, 0, -1.5000000000]) {
																	cube(center = true, size = [17.5500000000, 17.5500000000, 6.0000000000]);
																}
															}
														}
													}
												}
											}
										}
										translate(v = [95.2500000000, 0, 0]) {
											translate(v = [0, -57.1500000000, 0]) {
												union() {
													translate(v = [9.5250000000, 0, 0]) {
														translate(v = [0, -9.5250000000, 0]) {
															cube(center = true, size = [19.0500000000, 19.0500000000, 1.1110000000]);
														}
													}
													translate(v = [9.5250000000, 0, 0]) {
														translate(v = [0, -9.5250000000, 0]) {
															difference() {
																translate(v = [0, 0, -1.5000000000]) {
																	cube(center = true, size = [19.0500000000, 19.0500000000, 4.1110000000]);
																}
																translate(v = [0, 0, -1.5000000000]) {
																	cube(center = true, size = [17.5500000000, 17.5500000000, 6.0000000000]);
																}
															}
														}
													}
												}
											}
										}
										translate(v = [95.2500000000, 0, 0]) {
											translate(v = [0, -76.2000000000, 0]) {
												union() {
													translate(v = [9.5250000000, 0, 0]) {
														translate(v = [0, -9.5250000000, 0]) {
															cube(center = true, size = [19.0500000000, 19.0500000000, 1.1110000000]);
														}
													}
													translate(v = [9.5250000000, 0, 0]) {
														translate(v = [0, -9.5250000000, 0]) {
															difference() {
																translate(v = [0, 0, -1.5000000000]) {
																	cube(center = true, size = [19.0500000000, 19.0500000000, 4.1110000000]);
																}
																translate(v = [0, 0, -1.5000000000]) {
																	cube(center = true, size = [17.5500000000, 17.5500000000, 6.0000000000]);
																}
															}
														}
													}
												}
											}
										}
										translate(v = [114.3000000000, 0, 0]) {
											translate(v = [0, 0.0000000000, 0]) {
												union() {
													translate(v = [9.5250000000, 0, 0]) {
														translate(v = [0, -9.5250000000, 0]) {
															cube(center = true, size = [19.0500000000, 19.0500000000, 1.1110000000]);
														}
													}
													translate(v = [9.5250000000, 0, 0]) {
														translate(v = [0, -9.5250000000, 0]) {
															difference() {
																translate(v = [0, 0, -1.5000000000]) {
																	cube(center = true, size = [19.0500000000, 19.0500000000, 4.1110000000]);
																}
																translate(v = [0, 0, -1.5000000000]) {
																	cube(center = true, size = [17.5500000000, 17.5500000000, 6.0000000000]);
																}
															}
														}
													}
												}
											}
										}
										translate(v = [114.3000000000, 0, 0]) {
											translate(v = [0, -19.0500000000, 0]) {
												union() {
													translate(v = [9.5250000000, 0, 0]) {
														translate(v = [0, -9.5250000000, 0]) {
															cube(center = true, size = [19.0500000000, 19.0500000000, 1.1110000000]);
														}
													}
													translate(v = [9.5250000000, 0, 0]) {
														translate(v = [0, -9.5250000000, 0]) {
															difference() {
																translate(v = [0, 0, -1.5000000000]) {
																	cube(center = true, size = [19.0500000000, 19.0500000000, 4.1110000000]);
																}
																translate(v = [0, 0, -1.5000000000]) {
																	cube(center = true, size = [17.5500000000, 17.5500000000, 6.0000000000]);
																}
															}
														}
													}
												}
											}
										}
										translate(v = [114.3000000000, 0, 0]) {
											translate(v = [0, -38.1000000000, 0]) {
												union() {
													translate(v = [9.5250000000, 0, 0]) {
														translate(v = [0, -9.5250000000, 0]) {
															cube(center = true, size = [19.0500000000, 19.0500000000, 1.1110000000]);
														}
													}
													translate(v = [9.5250000000, 0, 0]) {
														translate(v = [0, -9.5250000000, 0]) {
															difference() {
																translate(v = [0, 0, -1.5000000000]) {
																	cube(center = true, size = [19.0500000000, 19.0500000000, 4.1110000000]);
																}
																translate(v = [0, 0, -1.5000000000]) {
																	cube(center = true, size = [17.5500000000, 17.5500000000, 6.0000000000]);
																}
															}
														}
													}
												}
											}
										}
										translate(v = [114.3000000000, 0, 0]) {
											translate(v = [0, -57.1500000000, 0]) {
												union() {
													translate(v = [9.5250000000, 0, 0]) {
														translate(v = [0, -9.5250000000, 0]) {
															cube(center = true, size = [19.0500000000, 19.0500000000, 1.1110000000]);
														}
													}
													translate(v = [9.5250000000, 0, 0]) {
														translate(v = [0, -9.5250000000, 0]) {
															difference() {
																translate(v = [0, 0, -1.5000000000]) {
																	cube(center = true, size = [19.0500000000, 19.0500000000, 4.1110000000]);
																}
																translate(v = [0, 0, -1.5000000000]) {
																	cube(center = true, size = [17.5500000000, 17.5500000000, 6.0000000000]);
																}
															}
														}
													}
												}
											}
										}
										translate(v = [114.3000000000, 0, 0]) {
											translate(v = [0, -76.2000000000, 0]) {
												union() {
													translate(v = [9.5250000000, 0, 0]) {
														translate(v = [0, -9.5250000000, 0]) {
															cube(center = true, size = [19.0500000000, 19.0500000000, 1.1110000000]);
														}
													}
													translate(v = [9.5250000000, 0, 0]) {
														translate(v = [0, -9.5250000000, 0]) {
															difference() {
																translate(v = [0, 0, -1.5000000000]) {
																	cube(center = true, size = [19.0500000000, 19.0500000000, 4.1110000000]);
																}
																translate(v = [0, 0, -1.5000000000]) {
																	cube(center = true, size = [17.5500000000, 17.5500000000, 6.0000000000]);
																}
															}
														}
													}
												}
											}
										}
										translate(v = [133.3500000000, 0, 0]) {
											translate(v = [0, 0.0000000000, 0]) {
												union() {
													translate(v = [9.5250000000, 0, 0]) {
														translate(v = [0, -9.5250000000, 0]) {
															cube(center = true, size = [19.0500000000, 19.0500000000, 1.1110000000]);
														}
													}
													translate(v = [9.5250000000, 0, 0]) {
														translate(v = [0, -9.5250000000, 0]) {
															difference() {
																translate(v = [0, 0, -1.5000000000]) {
																	cube(center = true, size = [19.0500000000, 19.0500000000, 4.1110000000]);
																}
																translate(v = [0, 0, -1.5000000000]) {
																	cube(center = true, size = [17.5500000000, 17.5500000000, 6.0000000000]);
																}
															}
														}
													}
												}
											}
										}
										translate(v = [133.3500000000, 0, 0]) {
											translate(v = [0, -19.0500000000, 0]) {
												union() {
													translate(v = [9.5250000000, 0, 0]) {
														translate(v = [0, -9.5250000000, 0]) {
															cube(center = true, size = [19.0500000000, 19.0500000000, 1.1110000000]);
														}
													}
													translate(v = [9.5250000000, 0, 0]) {
														translate(v = [0, -9.5250000000, 0]) {
															difference() {
																translate(v = [0, 0, -1.5000000000]) {
																	cube(center = true, size = [19.0500000000, 19.0500000000, 4.1110000000]);
																}
																translate(v = [0, 0, -1.5000000000]) {
																	cube(center = true, size = [17.5500000000, 17.5500000000, 6.0000000000]);
																}
															}
														}
													}
												}
											}
										}
										translate(v = [133.3500000000, 0, 0]) {
											translate(v = [0, -38.1000000000, 0]) {
												union() {
													translate(v = [9.5250000000, 0, 0]) {
														translate(v = [0, -9.5250000000, 0]) {
															cube(center = true, size = [19.0500000000, 19.0500000000, 1.1110000000]);
														}
													}
													translate(v = [9.5250000000, 0, 0]) {
														translate(v = [0, -9.5250000000, 0]) {
															difference() {
																translate(v = [0, 0, -1.5000000000]) {
																	cube(center = true, size = [19.0500000000, 19.0500000000, 4.1110000000]);
																}
																translate(v = [0, 0, -1.5000000000]) {
																	cube(center = true, size = [17.5500000000, 17.5500000000, 6.0000000000]);
																}
															}
														}
													}
												}
											}
										}
										translate(v = [133.3500000000, 0, 0]) {
											translate(v = [0, -57.1500000000, 0]) {
												union() {
													translate(v = [9.5250000000, 0, 0]) {
														translate(v = [0, -9.5250000000, 0]) {
															cube(center = true, size = [19.0500000000, 19.0500000000, 1.1110000000]);
														}
													}
													translate(v = [9.5250000000, 0, 0]) {
														translate(v = [0, -9.5250000000, 0]) {
															difference() {
																translate(v = [0, 0, -1.5000000000]) {
																	cube(center = true, size = [19.0500000000, 19.0500000000, 4.1110000000]);
																}
																translate(v = [0, 0, -1.5000000000]) {
																	cube(center = true, size = [17.5500000000, 17.5500000000, 6.0000000000]);
																}
															}
														}
													}
												}
											}
										}
										translate(v = [133.3500000000, 0, 0]) {
											translate(v = [0, -76.2000000000, 0]) {
												union() {
													translate(v = [9.5250000000, 0, 0]) {
														translate(v = [0, -9.5250000000, 0]) {
															cube(center = true, size = [19.0500000000, 19.0500000000, 1.1110000000]);
														}
													}
													translate(v = [9.5250000000, 0, 0]) {
														translate(v = [0, -9.5250000000, 0]) {
															difference() {
																translate(v = [0, 0, -1.5000000000]) {
																	cube(center = true, size = [19.0500000000, 19.0500000000, 4.1110000000]);
																}
																translate(v = [0, 0, -1.5000000000]) {
																	cube(center = true, size = [17.5500000000, 17.5500000000, 6.0000000000]);
																}
															}
														}
													}
												}
											}
										}
										translate(v = [152.4000000000, 0, 0]) {
											translate(v = [0, 0.0000000000, 0]) {
												union() {
													translate(v = [9.5250000000, 0, 0]) {
														translate(v = [0, -9.5250000000, 0]) {
															cube(center = true, size = [19.0500000000, 19.0500000000, 1.1110000000]);
														}
													}
													translate(v = [9.5250000000, 0, 0]) {
														translate(v = [0, -9.5250000000, 0]) {
															difference() {
																translate(v = [0, 0, -1.5000000000]) {
																	cube(center = true, size = [19.0500000000, 19.0500000000, 4.1110000000]);
																}
																translate(v = [0, 0, -1.5000000000]) {
																	cube(center = true, size = [17.5500000000, 17.5500000000, 6.0000000000]);
																}
															}
														}
													}
												}
											}
										}
										translate(v = [152.4000000000, 0, 0]) {
											translate(v = [0, -19.0500000000, 0]) {
												union() {
													translate(v = [9.5250000000, 0, 0]) {
														translate(v = [0, -9.5250000000, 0]) {
															cube(center = true, size = [19.0500000000, 19.0500000000, 1.1110000000]);
														}
													}
													translate(v = [9.5250000000, 0, 0]) {
														translate(v = [0, -9.5250000000, 0]) {
															difference() {
																translate(v = [0, 0, -1.5000000000]) {
																	cube(center = true, size = [19.0500000000, 19.0500000000, 4.1110000000]);
																}
																translate(v = [0, 0, -1.5000000000]) {
																	cube(center = true, size = [17.5500000000, 17.5500000000, 6.0000000000]);
																}
															}
														}
													}
												}
											}
										}
										translate(v = [152.4000000000, 0, 0]) {
											translate(v = [0, -38.1000000000, 0]) {
												union() {
													translate(v = [9.5250000000, 0, 0]) {
														translate(v = [0, -9.5250000000, 0]) {
															cube(center = true, size = [19.0500000000, 19.0500000000, 1.1110000000]);
														}
													}
													translate(v = [9.5250000000, 0, 0]) {
														translate(v = [0, -9.5250000000, 0]) {
															difference() {
																translate(v = [0, 0, -1.5000000000]) {
																	cube(center = true, size = [19.0500000000, 19.0500000000, 4.1110000000]);
																}
																translate(v = [0, 0, -1.5000000000]) {
																	cube(center = true, size = [17.5500000000, 17.5500000000, 6.0000000000]);
																}
															}
														}
													}
												}
											}
										}
										translate(v = [152.4000000000, 0, 0]) {
											translate(v = [0, -57.1500000000, 0]) {
												union() {
													translate(v = [9.5250000000, 0, 0]) {
														translate(v = [0, -9.5250000000, 0]) {
															cube(center = true, size = [19.0500000000, 19.0500000000, 1.1110000000]);
														}
													}
													translate(v = [9.5250000000, 0, 0]) {
														translate(v = [0, -9.5250000000, 0]) {
															difference() {
																translate(v = [0, 0, -1.5000000000]) {
																	cube(center = true, size = [19.0500000000, 19.0500000000, 4.1110000000]);
																}
																translate(v = [0, 0, -1.5000000000]) {
																	cube(center = true, size = [17.5500000000, 17.5500000000, 6.0000000000]);
																}
															}
														}
													}
												}
											}
										}
										translate(v = [152.4000000000, 0, 0]) {
											translate(v = [0, -76.2000000000, 0]) {
												union() {
													translate(v = [9.5250000000, 0, 0]) {
														translate(v = [0, -9.5250000000, 0]) {
															cube(center = true, size = [19.0500000000, 19.0500000000, 1.1110000000]);
														}
													}
													translate(v = [9.5250000000, 0, 0]) {
														translate(v = [0, -9.5250000000, 0]) {
															difference() {
																translate(v = [0, 0, -1.5000000000]) {
																	cube(center = true, size = [19.0500000000, 19.0500000000, 4.1110000000]);
																}
																translate(v = [0, 0, -1.5000000000]) {
																	cube(center = true, size = [17.5500000000, 17.5500000000, 6.0000000000]);
																}
															}
														}
													}
												}
											}
										}
										translate(v = [171.4500000000, 0, 0]) {
											translate(v = [0, 0.0000000000, 0]) {
												union() {
													translate(v = [9.5250000000, 0, 0]) {
														translate(v = [0, -9.5250000000, 0]) {
															cube(center = true, size = [19.0500000000, 19.0500000000, 1.1110000000]);
														}
													}
													translate(v = [9.5250000000, 0, 0]) {
														translate(v = [0, -9.5250000000, 0]) {
															difference() {
																translate(v = [0, 0, -1.5000000000]) {
																	cube(center = true, size = [19.0500000000, 19.0500000000, 4.1110000000]);
																}
																translate(v = [0, 0, -1.5000000000]) {
																	cube(center = true, size = [17.5500000000, 17.5500000000, 6.0000000000]);
																}
															}
														}
													}
												}
											}
										}
										translate(v = [171.4500000000, 0, 0]) {
											translate(v = [0, -19.0500000000, 0]) {
												union() {
													translate(v = [9.5250000000, 0, 0]) {
														translate(v = [0, -9.5250000000, 0]) {
															cube(center = true, size = [19.0500000000, 19.0500000000, 1.1110000000]);
														}
													}
													translate(v = [9.5250000000, 0, 0]) {
														translate(v = [0, -9.5250000000, 0]) {
															difference() {
																translate(v = [0, 0, -1.5000000000]) {
																	cube(center = true, size = [19.0500000000, 19.0500000000, 4.1110000000]);
																}
																translate(v = [0, 0, -1.5000000000]) {
																	cube(center = true, size = [17.5500000000, 17.5500000000, 6.0000000000]);
																}
															}
														}
													}
												}
											}
										}
										translate(v = [171.4500000000, 0, 0]) {
											translate(v = [0, -38.1000000000, 0]) {
												union() {
													translate(v = [9.5250000000, 0, 0]) {
														translate(v = [0, -9.5250000000, 0]) {
															cube(center = true, size = [19.0500000000, 19.0500000000, 1.1110000000]);
														}
													}
													translate(v = [9.5250000000, 0, 0]) {
														translate(v = [0, -9.5250000000, 0]) {
															difference() {
																translate(v = [0, 0, -1.5000000000]) {
																	cube(center = true, size = [19.0500000000, 19.0500000000, 4.1110000000]);
																}
																translate(v = [0, 0, -1.5000000000]) {
																	cube(center = true, size = [17.5500000000, 17.5500000000, 6.0000000000]);
																}
															}
														}
													}
												}
											}
										}
										translate(v = [171.4500000000, 0, 0]) {
											translate(v = [0, -57.1500000000, 0]) {
												union() {
													translate(v = [9.5250000000, 0, 0]) {
														translate(v = [0, -9.5250000000, 0]) {
															cube(center = true, size = [19.0500000000, 19.0500000000, 1.1110000000]);
														}
													}
													translate(v = [9.5250000000, 0, 0]) {
														translate(v = [0, -9.5250000000, 0]) {
															difference() {
																translate(v = [0, 0, -1.5000000000]) {
																	cube(center = true, size = [19.0500000000, 19.0500000000, 4.1110000000]);
																}
																translate(v = [0, 0, -1.5000000000]) {
																	cube(center = true, size = [17.5500000000, 17.5500000000, 6.0000000000]);
																}
															}
														}
													}
												}
											}
										}
										translate(v = [171.4500000000, 0, 0]) {
											translate(v = [0, -76.2000000000, 0]) {
												union() {
													translate(v = [9.5250000000, 0, 0]) {
														translate(v = [0, -9.5250000000, 0]) {
															cube(center = true, size = [19.0500000000, 19.0500000000, 1.1110000000]);
														}
													}
													translate(v = [9.5250000000, 0, 0]) {
														translate(v = [0, -9.5250000000, 0]) {
															difference() {
																translate(v = [0, 0, -1.5000000000]) {
																	cube(center = true, size = [19.0500000000, 19.0500000000, 4.1110000000]);
																}
																translate(v = [0, 0, -1.5000000000]) {
																	cube(center = true, size = [17.5500000000, 17.5500000000, 6.0000000000]);
																}
															}
														}
													}
												}
											}
										}
										translate(v = [190.5000000000, 0, 0]) {
											translate(v = [0, 0.0000000000, 0]) {
												union() {
													translate(v = [9.5250000000, 0, 0]) {
														translate(v = [0, -9.5250000000, 0]) {
															cube(center = true, size = [19.0500000000, 19.0500000000, 1.1110000000]);
														}
													}
													translate(v = [9.5250000000, 0, 0]) {
														translate(v = [0, -9.5250000000, 0]) {
															difference() {
																translate(v = [0, 0, -1.5000000000]) {
																	cube(center = true, size = [19.0500000000, 19.0500000000, 4.1110000000]);
																}
																translate(v = [0, 0, -1.5000000000]) {
																	cube(center = true, size = [17.5500000000, 17.5500000000, 6.0000000000]);
																}
															}
														}
													}
												}
											}
										}
										translate(v = [190.5000000000, 0, 0]) {
											translate(v = [0, -19.0500000000, 0]) {
												union() {
													translate(v = [9.5250000000, 0, 0]) {
														translate(v = [0, -9.5250000000, 0]) {
															cube(center = true, size = [19.0500000000, 19.0500000000, 1.1110000000]);
														}
													}
													translate(v = [9.5250000000, 0, 0]) {
														translate(v = [0, -9.5250000000, 0]) {
															difference() {
																translate(v = [0, 0, -1.5000000000]) {
																	cube(center = true, size = [19.0500000000, 19.0500000000, 4.1110000000]);
																}
																translate(v = [0, 0, -1.5000000000]) {
																	cube(center = true, size = [17.5500000000, 17.5500000000, 6.0000000000]);
																}
															}
														}
													}
												}
											}
										}
										translate(v = [190.5000000000, 0, 0]) {
											translate(v = [0, -38.1000000000, 0]) {
												union() {
													translate(v = [9.5250000000, 0, 0]) {
														translate(v = [0, -9.5250000000, 0]) {
															cube(center = true, size = [19.0500000000, 19.0500000000, 1.1110000000]);
														}
													}
													translate(v = [9.5250000000, 0, 0]) {
														translate(v = [0, -9.5250000000, 0]) {
															difference() {
																translate(v = [0, 0, -1.5000000000]) {
																	cube(center = true, size = [19.0500000000, 19.0500000000, 4.1110000000]);
																}
																translate(v = [0, 0, -1.5000000000]) {
																	cube(center = true, size = [17.5500000000, 17.5500000000, 6.0000000000]);
																}
															}
														}
													}
												}
											}
										}
										translate(v = [190.5000000000, 0, 0]) {
											translate(v = [0, -57.1500000000, 0]) {
												union() {
													translate(v = [9.5250000000, 0, 0]) {
														translate(v = [0, -9.5250000000, 0]) {
															cube(center = true, size = [19.0500000000, 19.0500000000, 1.1110000000]);
														}
													}
													translate(v = [9.5250000000, 0, 0]) {
														translate(v = [0, -9.5250000000, 0]) {
															difference() {
																translate(v = [0, 0, -1.5000000000]) {
																	cube(center = true, size = [19.0500000000, 19.0500000000, 4.1110000000]);
																}
																translate(v = [0, 0, -1.5000000000]) {
																	cube(center = true, size = [17.5500000000, 17.5500000000, 6.0000000000]);
																}
															}
														}
													}
												}
											}
										}
										translate(v = [190.5000000000, 0, 0]) {
											translate(v = [0, -76.2000000000, 0]) {
												union() {
													translate(v = [9.5250000000, 0, 0]) {
														translate(v = [0, -9.5250000000, 0]) {
															cube(center = true, size = [19.0500000000, 19.0500000000, 1.1110000000]);
														}
													}
													translate(v = [9.5250000000, 0, 0]) {
														translate(v = [0, -9.5250000000, 0]) {
															difference() {
																translate(v = [0, 0, -1.5000000000]) {
																	cube(center = true, size = [19.0500000000, 19.0500000000, 4.1110000000]);
																}
																translate(v = [0, 0, -1.5000000000]) {
																	cube(center = true, size = [17.5500000000, 17.5500000000, 6.0000000000]);
																}
															}
														}
													}
												}
											}
										}
										translate(v = [209.5500000000, 0, 0]) {
											translate(v = [0, 0.0000000000, 0]) {
												union() {
													translate(v = [9.5250000000, 0, 0]) {
														translate(v = [0, -9.5250000000, 0]) {
															cube(center = true, size = [19.0500000000, 19.0500000000, 1.1110000000]);
														}
													}
													translate(v = [9.5250000000, 0, 0]) {
														translate(v = [0, -9.5250000000, 0]) {
															difference() {
																translate(v = [0, 0, -1.5000000000]) {
																	cube(center = true, size = [19.0500000000, 19.0500000000, 4.1110000000]);
																}
																translate(v = [0, 0, -1.5000000000]) {
																	cube(center = true, size = [17.5500000000, 17.5500000000, 6.0000000000]);
																}
															}
														}
													}
												}
											}
										}
										translate(v = [209.5500000000, 0, 0]) {
											translate(v = [0, -19.0500000000, 0]) {
												union() {
													translate(v = [9.5250000000, 0, 0]) {
														translate(v = [0, -9.5250000000, 0]) {
															cube(center = true, size = [19.0500000000, 19.0500000000, 1.1110000000]);
														}
													}
													translate(v = [9.5250000000, 0, 0]) {
														translate(v = [0, -9.5250000000, 0]) {
															difference() {
																translate(v = [0, 0, -1.5000000000]) {
																	cube(center = true, size = [19.0500000000, 19.0500000000, 4.1110000000]);
																}
																translate(v = [0, 0, -1.5000000000]) {
																	cube(center = true, size = [17.5500000000, 17.5500000000, 6.0000000000]);
																}
															}
														}
													}
												}
											}
										}
										translate(v = [209.5500000000, 0, 0]) {
											translate(v = [0, -38.1000000000, 0]) {
												union() {
													translate(v = [9.5250000000, 0, 0]) {
														translate(v = [0, -9.5250000000, 0]) {
															cube(center = true, size = [19.0500000000, 19.0500000000, 1.1110000000]);
														}
													}
													translate(v = [9.5250000000, 0, 0]) {
														translate(v = [0, -9.5250000000, 0]) {
															difference() {
																translate(v = [0, 0, -1.5000000000]) {
																	cube(center = true, size = [19.0500000000, 19.0500000000, 4.1110000000]);
																}
																translate(v = [0, 0, -1.5000000000]) {
																	cube(center = true, size = [17.5500000000, 17.5500000000, 6.0000000000]);
																}
															}
														}
													}
												}
											}
										}
										translate(v = [209.5500000000, 0, 0]) {
											translate(v = [0, -57.1500000000, 0]) {
												union() {
													translate(v = [9.5250000000, 0, 0]) {
														translate(v = [0, -9.5250000000, 0]) {
															cube(center = true, size = [19.0500000000, 19.0500000000, 1.1110000000]);
														}
													}
													translate(v = [9.5250000000, 0, 0]) {
														translate(v = [0, -9.5250000000, 0]) {
															difference() {
																translate(v = [0, 0, -1.5000000000]) {
																	cube(center = true, size = [19.0500000000, 19.0500000000, 4.1110000000]);
																}
																translate(v = [0, 0, -1.5000000000]) {
																	cube(center = true, size = [17.5500000000, 17.5500000000, 6.0000000000]);
																}
															}
														}
													}
												}
											}
										}
										translate(v = [209.5500000000, 0, 0]) {
											translate(v = [0, -76.2000000000, 0]) {
												union() {
													translate(v = [9.5250000000, 0, 0]) {
														translate(v = [0, -9.5250000000, 0]) {
															cube(center = true, size = [19.0500000000, 19.0500000000, 1.1110000000]);
														}
													}
													translate(v = [9.5250000000, 0, 0]) {
														translate(v = [0, -9.5250000000, 0]) {
															difference() {
																translate(v = [0, 0, -1.5000000000]) {
																	cube(center = true, size = [19.0500000000, 19.0500000000, 4.1110000000]);
																}
																translate(v = [0, 0, -1.5000000000]) {
																	cube(center = true, size = [17.5500000000, 17.5500000000, 6.0000000000]);
																}
															}
														}
													}
												}
											}
										}
										translate(v = [228.6000000000, 0, 0]) {
											translate(v = [0, 0.0000000000, 0]) {
												union() {
													translate(v = [9.5250000000, 0, 0]) {
														translate(v = [0, -9.5250000000, 0]) {
															cube(center = true, size = [19.0500000000, 19.0500000000, 1.1110000000]);
														}
													}
													translate(v = [9.5250000000, 0, 0]) {
														translate(v = [0, -9.5250000000, 0]) {
															difference() {
																translate(v = [0, 0, -1.5000000000]) {
																	cube(center = true, size = [19.0500000000, 19.0500000000, 4.1110000000]);
																}
																translate(v = [0, 0, -1.5000000000]) {
																	cube(center = true, size = [17.5500000000, 17.5500000000, 6.0000000000]);
																}
															}
														}
													}
												}
											}
										}
										translate(v = [228.6000000000, 0, 0]) {
											translate(v = [0, -19.0500000000, 0]) {
												union() {
													translate(v = [9.5250000000, 0, 0]) {
														translate(v = [0, -9.5250000000, 0]) {
															cube(center = true, size = [19.0500000000, 19.0500000000, 1.1110000000]);
														}
													}
													translate(v = [9.5250000000, 0, 0]) {
														translate(v = [0, -9.5250000000, 0]) {
															difference() {
																translate(v = [0, 0, -1.5000000000]) {
																	cube(center = true, size = [19.0500000000, 19.0500000000, 4.1110000000]);
																}
																translate(v = [0, 0, -1.5000000000]) {
																	cube(center = true, size = [17.5500000000, 17.5500000000, 6.0000000000]);
																}
															}
														}
													}
												}
											}
										}
										translate(v = [228.6000000000, 0, 0]) {
											translate(v = [0, -38.1000000000, 0]) {
												union() {
													translate(v = [9.5250000000, 0, 0]) {
														translate(v = [0, -9.5250000000, 0]) {
															cube(center = true, size = [19.0500000000, 19.0500000000, 1.1110000000]);
														}
													}
													translate(v = [9.5250000000, 0, 0]) {
														translate(v = [0, -9.5250000000, 0]) {
															difference() {
																translate(v = [0, 0, -1.5000000000]) {
																	cube(center = true, size = [19.0500000000, 19.0500000000, 4.1110000000]);
																}
																translate(v = [0, 0, -1.5000000000]) {
																	cube(center = true, size = [17.5500000000, 17.5500000000, 6.0000000000]);
																}
															}
														}
													}
												}
											}
										}
										translate(v = [228.6000000000, 0, 0]) {
											translate(v = [0, -57.1500000000, 0]) {
												union() {
													translate(v = [9.5250000000, 0, 0]) {
														translate(v = [0, -9.5250000000, 0]) {
															cube(center = true, size = [19.0500000000, 19.0500000000, 1.1110000000]);
														}
													}
													translate(v = [9.5250000000, 0, 0]) {
														translate(v = [0, -9.5250000000, 0]) {
															difference() {
																translate(v = [0, 0, -1.5000000000]) {
																	cube(center = true, size = [19.0500000000, 19.0500000000, 4.1110000000]);
																}
																translate(v = [0, 0, -1.5000000000]) {
																	cube(center = true, size = [17.5500000000, 17.5500000000, 6.0000000000]);
																}
															}
														}
													}
												}
											}
										}
										translate(v = [228.6000000000, 0, 0]) {
											translate(v = [0, -76.2000000000, 0]) {
												union() {
													translate(v = [9.5250000000, 0, 0]) {
														translate(v = [0, -9.5250000000, 0]) {
															cube(center = true, size = [19.0500000000, 19.0500000000, 1.1110000000]);
														}
													}
													translate(v = [9.5250000000, 0, 0]) {
														translate(v = [0, -9.5250000000, 0]) {
															difference() {
																translate(v = [0, 0, -1.5000000000]) {
																	cube(center = true, size = [19.0500000000, 19.0500000000, 4.1110000000]);
																}
																translate(v = [0, 0, -1.5000000000]) {
																	cube(center = true, size = [17.5500000000, 17.5500000000, 6.0000000000]);
																}
															}
														}
													}
												}
											}
										}
										translate(v = [247.6500000000, 0, 0]) {
											translate(v = [0, 0.0000000000, 0]) {
												union() {
													translate(v = [9.5250000000, 0, 0]) {
														translate(v = [0, -9.5250000000, 0]) {
															cube(center = true, size = [19.0500000000, 19.0500000000, 1.1110000000]);
														}
													}
													translate(v = [9.5250000000, 0, 0]) {
														translate(v = [0, -9.5250000000, 0]) {
															difference() {
																translate(v = [0, 0, -1.5000000000]) {
																	cube(center = true, size = [19.0500000000, 19.0500000000, 4.1110000000]);
																}
																translate(v = [0, 0, -1.5000000000]) {
																	cube(center = true, size = [17.5500000000, 17.5500000000, 6.0000000000]);
																}
															}
														}
													}
												}
											}
										}
										translate(v = [247.6500000000, 0, 0]) {
											translate(v = [0, -19.0500000000, 0]) {
												union() {
													translate(v = [9.5250000000, 0, 0]) {
														translate(v = [0, -9.5250000000, 0]) {
															cube(center = true, size = [19.0500000000, 19.0500000000, 1.1110000000]);
														}
													}
													translate(v = [9.5250000000, 0, 0]) {
														translate(v = [0, -9.5250000000, 0]) {
															difference() {
																translate(v = [0, 0, -1.5000000000]) {
																	cube(center = true, size = [19.0500000000, 19.0500000000, 4.1110000000]);
																}
																translate(v = [0, 0, -1.5000000000]) {
																	cube(center = true, size = [17.5500000000, 17.5500000000, 6.0000000000]);
																}
															}
														}
													}
												}
											}
										}
										translate(v = [247.6500000000, 0, 0]) {
											translate(v = [0, -38.1000000000, 0]) {
												union() {
													translate(v = [9.5250000000, 0, 0]) {
														translate(v = [0, -9.5250000000, 0]) {
															cube(center = true, size = [19.0500000000, 19.0500000000, 1.1110000000]);
														}
													}
													translate(v = [9.5250000000, 0, 0]) {
														translate(v = [0, -9.5250000000, 0]) {
															difference() {
																translate(v = [0, 0, -1.5000000000]) {
																	cube(center = true, size = [19.0500000000, 19.0500000000, 4.1110000000]);
																}
																translate(v = [0, 0, -1.5000000000]) {
																	cube(center = true, size = [17.5500000000, 17.5500000000, 6.0000000000]);
																}
															}
														}
													}
												}
											}
										}
										translate(v = [247.6500000000, 0, 0]) {
											translate(v = [0, -57.1500000000, 0]) {
												union() {
													translate(v = [9.5250000000, 0, 0]) {
														translate(v = [0, -9.5250000000, 0]) {
															cube(center = true, size = [19.0500000000, 19.0500000000, 1.1110000000]);
														}
													}
													translate(v = [9.5250000000, 0, 0]) {
														translate(v = [0, -9.5250000000, 0]) {
															difference() {
																translate(v = [0, 0, -1.5000000000]) {
																	cube(center = true, size = [19.0500000000, 19.0500000000, 4.1110000000]);
																}
																translate(v = [0, 0, -1.5000000000]) {
																	cube(center = true, size = [17.5500000000, 17.5500000000, 6.0000000000]);
																}
															}
														}
													}
												}
											}
										}
										translate(v = [247.6500000000, 0, 0]) {
											translate(v = [0, -76.2000000000, 0]) {
												union() {
													translate(v = [9.5250000000, 0, 0]) {
														translate(v = [0, -9.5250000000, 0]) {
															cube(center = true, size = [19.0500000000, 19.0500000000, 1.1110000000]);
														}
													}
													translate(v = [9.5250000000, 0, 0]) {
														translate(v = [0, -9.5250000000, 0]) {
															difference() {
																translate(v = [0, 0, -1.5000000000]) {
																	cube(center = true, size = [19.0500000000, 19.0500000000, 4.1110000000]);
																}
																translate(v = [0, 0, -1.5000000000]) {
																	cube(center = true, size = [17.5500000000, 17.5500000000, 6.0000000000]);
																}
															}
														}
													}
												}
											}
										}
										translate(v = [266.7000000000, 0, 0]) {
											translate(v = [0, 0.0000000000, 0]) {
												union() {
													translate(v = [9.5250000000, 0, 0]) {
														translate(v = [0, -9.5250000000, 0]) {
															cube(center = true, size = [19.0500000000, 19.0500000000, 1.1110000000]);
														}
													}
													translate(v = [9.5250000000, 0, 0]) {
														translate(v = [0, -9.5250000000, 0]) {
															difference() {
																translate(v = [0, 0, -1.5000000000]) {
																	cube(center = true, size = [19.0500000000, 19.0500000000, 4.1110000000]);
																}
																translate(v = [0, 0, -1.5000000000]) {
																	cube(center = true, size = [17.5500000000, 17.5500000000, 6.0000000000]);
																}
															}
														}
													}
												}
											}
										}
										translate(v = [266.7000000000, 0, 0]) {
											translate(v = [0, -19.0500000000, 0]) {
												union() {
													translate(v = [9.5250000000, 0, 0]) {
														translate(v = [0, -9.5250000000, 0]) {
															cube(center = true, size = [19.0500000000, 19.0500000000, 1.1110000000]);
														}
													}
													translate(v = [9.5250000000, 0, 0]) {
														translate(v = [0, -9.5250000000, 0]) {
															difference() {
																translate(v = [0, 0, -1.5000000000]) {
																	cube(center = true, size = [19.0500000000, 19.0500000000, 4.1110000000]);
																}
																translate(v = [0, 0, -1.5000000000]) {
																	cube(center = true, size = [17.5500000000, 17.5500000000, 6.0000000000]);
																}
															}
														}
													}
												}
											}
										}
										translate(v = [266.7000000000, 0, 0]) {
											translate(v = [0, -38.1000000000, 0]) {
												union() {
													translate(v = [9.5250000000, 0, 0]) {
														translate(v = [0, -9.5250000000, 0]) {
															cube(center = true, size = [19.0500000000, 19.0500000000, 1.1110000000]);
														}
													}
													translate(v = [9.5250000000, 0, 0]) {
														translate(v = [0, -9.5250000000, 0]) {
															difference() {
																translate(v = [0, 0, -1.5000000000]) {
																	cube(center = true, size = [19.0500000000, 19.0500000000, 4.1110000000]);
																}
																translate(v = [0, 0, -1.5000000000]) {
																	cube(center = true, size = [17.5500000000, 17.5500000000, 6.0000000000]);
																}
															}
														}
													}
												}
											}
										}
										translate(v = [266.7000000000, 0, 0]) {
											translate(v = [0, -57.1500000000, 0]) {
												union() {
													translate(v = [9.5250000000, 0, 0]) {
														translate(v = [0, -9.5250000000, 0]) {
															cube(center = true, size = [19.0500000000, 19.0500000000, 1.1110000000]);
														}
													}
													translate(v = [9.5250000000, 0, 0]) {
														translate(v = [0, -9.5250000000, 0]) {
															difference() {
																translate(v = [0, 0, -1.5000000000]) {
																	cube(center = true, size = [19.0500000000, 19.0500000000, 4.1110000000]);
																}
																translate(v = [0, 0, -1.5000000000]) {
																	cube(center = true, size = [17.5500000000, 17.5500000000, 6.0000000000]);
																}
															}
														}
													}
												}
											}
										}
										translate(v = [266.7000000000, 0, 0]) {
											translate(v = [0, -76.2000000000, 0]) {
												union() {
													translate(v = [9.5250000000, 0, 0]) {
														translate(v = [0, -9.5250000000, 0]) {
															cube(center = true, size = [19.0500000000, 19.0500000000, 1.1110000000]);
														}
													}
													translate(v = [9.5250000000, 0, 0]) {
														translate(v = [0, -9.5250000000, 0]) {
															difference() {
																translate(v = [0, 0, -1.5000000000]) {
																	cube(center = true, size = [19.0500000000, 19.0500000000, 4.1110000000]);
																}
																translate(v = [0, 0, -1.5000000000]) {
																	cube(center = true, size = [17.5500000000, 17.5500000000, 6.0000000000]);
																}
															}
														}
													}
												}
											}
										}
										translate(v = [0, 0, -35.5000000000]) {
											translate(v = [142.8750000000, 0, 0]) {
												translate(v = [0, -47.6250000000, 0]) {
													difference() {
														minkowski() {
															cube(center = true, size = [284.7500000000, 94.2500000000, 71]);
															cylinder(center = true, h = 0.5555000000, r = 4);
														}
														minkowski() {
															cube(center = true, size = [278.7500000000, 88.2500000000, 142]);
															cube(center = true, size = [8, 8, 0.5555000000]);
														}
													}
												}
											}
										}
									}
								}
								union() {
									union() {
										translate(v = [0.0000000000, 0, 0]) {
											translate(v = [0, -76.2000000000, 0]) {
												translate(v = [11.9062500000, 0, 0]) {
													translate(v = [0, -9.5250000000, 0]) {
														translate(v = [0, 0, -1.5000000000]) {
															cube(center = true, size = [23.8125000000, 19.0500000000, 4.1110000000]);
														}
													}
												}
											}
										}
										translate(v = [0.0000000000, 0, 0]) {
											translate(v = [0, -57.1500000000, 0]) {
												translate(v = [14.2875000000, 0, 0]) {
													translate(v = [0, -9.5250000000, 0]) {
														translate(v = [0, 0, -1.5000000000]) {
															cube(center = true, size = [28.5750000000, 19.0500000000, 4.1110000000]);
														}
													}
												}
											}
										}
										translate(v = [0.0000000000, 0, 0]) {
											translate(v = [0, -38.1000000000, 0]) {
												translate(v = [17.4307500000, 0, 0]) {
													translate(v = [0, -9.5250000000, 0]) {
														translate(v = [0, 0, -1.5000000000]) {
															cube(center = true, size = [34.8615000000, 19.0500000000, 4.1110000000]);
														}
													}
												}
											}
										}
										translate(v = [0.0000000000, 0, 0]) {
											translate(v = [0, -19.0500000000, 0]) {
												translate(v = [11.1442500000, 0, 0]) {
													translate(v = [0, -9.5250000000, 0]) {
														translate(v = [0, 0, -1.5000000000]) {
															cube(center = true, size = [22.2885000000, 19.0500000000, 4.1110000000]);
														}
													}
												}
											}
										}
										translate(v = [0.0000000000, 0, 0]) {
											translate(v = [0, -0.0000000000, 0]) {
												translate(v = [14.2875000000, 0, 0]) {
													translate(v = [0, -9.5250000000, 0]) {
														translate(v = [0, 0, -1.5000000000]) {
															cube(center = true, size = [28.5750000000, 19.0500000000, 4.1110000000]);
														}
													}
												}
											}
										}
										translate(v = [22.2885000000, 0, 0]) {
											translate(v = [0, -19.0500000000, 0]) {
												translate(v = [9.5250000000, 0, 0]) {
													translate(v = [0, -9.5250000000, 0]) {
														translate(v = [0, 0, -1.5000000000]) {
															cube(center = true, size = [19.0500000000, 19.0500000000, 4.1110000000]);
														}
													}
												}
											}
										}
										translate(v = [23.8125000000, 0, 0]) {
											translate(v = [0, -76.2000000000, 0]) {
												translate(v = [9.5250000000, 0, 0]) {
													translate(v = [0, -9.5250000000, 0]) {
														translate(v = [0, 0, -1.5000000000]) {
															cube(center = true, size = [19.0500000000, 19.0500000000, 4.1110000000]);
														}
													}
												}
											}
										}
										translate(v = [28.5750000000, 0, 0]) {
											translate(v = [0, -57.1500000000, 0]) {
												translate(v = [9.5250000000, 0, 0]) {
													translate(v = [0, -9.5250000000, 0]) {
														translate(v = [0, 0, -1.5000000000]) {
															cube(center = true, size = [19.0500000000, 19.0500000000, 4.1110000000]);
														}
													}
												}
											}
										}
										translate(v = [28.5750000000, 0, 0]) {
											translate(v = [0, -0.0000000000, 0]) {
												translate(v = [9.5250000000, 0, 0]) {
													translate(v = [0, -9.5250000000, 0]) {
														translate(v = [0, 0, -1.5000000000]) {
															cube(center = true, size = [19.0500000000, 19.0500000000, 4.1110000000]);
														}
													}
												}
											}
										}
										translate(v = [34.8615000000, 0, 0]) {
											translate(v = [0, -38.1000000000, 0]) {
												translate(v = [9.5250000000, 0, 0]) {
													translate(v = [0, -9.5250000000, 0]) {
														translate(v = [0, 0, -1.5000000000]) {
															cube(center = true, size = [19.0500000000, 19.0500000000, 4.1110000000]);
														}
													}
												}
											}
										}
										translate(v = [41.3385000000, 0, 0]) {
											translate(v = [0, -19.0500000000, 0]) {
												translate(v = [9.5250000000, 0, 0]) {
													translate(v = [0, -9.5250000000, 0]) {
														translate(v = [0, 0, -1.5000000000]) {
															cube(center = true, size = [19.0500000000, 19.0500000000, 4.1110000000]);
														}
													}
												}
											}
										}
										translate(v = [42.8625000000, 0, 0]) {
											translate(v = [0, -76.2000000000, 0]) {
												translate(v = [9.5250000000, 0, 0]) {
													translate(v = [0, -9.5250000000, 0]) {
														translate(v = [0, 0, -1.5000000000]) {
															cube(center = true, size = [19.0500000000, 19.0500000000, 4.1110000000]);
														}
													}
												}
											}
										}
										translate(v = [47.6250000000, 0, 0]) {
											translate(v = [0, -57.1500000000, 0]) {
												translate(v = [9.5250000000, 0, 0]) {
													translate(v = [0, -9.5250000000, 0]) {
														translate(v = [0, 0, -1.5000000000]) {
															cube(center = true, size = [19.0500000000, 19.0500000000, 4.1110000000]);
														}
													}
												}
											}
										}
										translate(v = [47.6250000000, 0, 0]) {
											translate(v = [0, -0.0000000000, 0]) {
												translate(v = [9.5250000000, 0, 0]) {
													translate(v = [0, -9.5250000000, 0]) {
														translate(v = [0, 0, -1.5000000000]) {
															cube(center = true, size = [19.0500000000, 19.0500000000, 4.1110000000]);
														}
													}
												}
											}
										}
										translate(v = [53.9115000000, 0, 0]) {
											translate(v = [0, -38.1000000000, 0]) {
												translate(v = [9.5250000000, 0, 0]) {
													translate(v = [0, -9.5250000000, 0]) {
														translate(v = [0, 0, -1.5000000000]) {
															cube(center = true, size = [19.0500000000, 19.0500000000, 4.1110000000]);
														}
													}
												}
											}
										}
										translate(v = [60.3885000000, 0, 0]) {
											translate(v = [0, -19.0500000000, 0]) {
												translate(v = [9.5250000000, 0, 0]) {
													translate(v = [0, -9.5250000000, 0]) {
														translate(v = [0, 0, -1.5000000000]) {
															cube(center = true, size = [19.0500000000, 19.0500000000, 4.1110000000]);
														}
													}
												}
											}
										}
										translate(v = [61.9125000000, 0, 0]) {
											translate(v = [0, -76.2000000000, 0]) {
												translate(v = [11.9062500000, 0, 0]) {
													translate(v = [0, -9.5250000000, 0]) {
														translate(v = [0, 0, -1.5000000000]) {
															cube(center = true, size = [23.8125000000, 19.0500000000, 4.1110000000]);
														}
													}
												}
											}
										}
										translate(v = [66.6750000000, 0, 0]) {
											translate(v = [0, -57.1500000000, 0]) {
												translate(v = [9.5250000000, 0, 0]) {
													translate(v = [0, -9.5250000000, 0]) {
														translate(v = [0, 0, -1.5000000000]) {
															cube(center = true, size = [19.0500000000, 19.0500000000, 4.1110000000]);
														}
													}
												}
											}
										}
										translate(v = [66.6750000000, 0, 0]) {
											translate(v = [0, -0.0000000000, 0]) {
												translate(v = [9.5250000000, 0, 0]) {
													translate(v = [0, -9.5250000000, 0]) {
														translate(v = [0, 0, -1.5000000000]) {
															cube(center = true, size = [19.0500000000, 19.0500000000, 4.1110000000]);
														}
													}
												}
											}
										}
										translate(v = [72.9615000000, 0, 0]) {
											translate(v = [0, -38.1000000000, 0]) {
												translate(v = [9.5250000000, 0, 0]) {
													translate(v = [0, -9.5250000000, 0]) {
														translate(v = [0, 0, -1.5000000000]) {
															cube(center = true, size = [19.0500000000, 19.0500000000, 4.1110000000]);
														}
													}
												}
											}
										}
										translate(v = [79.4385000000, 0, 0]) {
											translate(v = [0, -19.0500000000, 0]) {
												translate(v = [9.5250000000, 0, 0]) {
													translate(v = [0, -9.5250000000, 0]) {
														translate(v = [0, 0, -1.5000000000]) {
															cube(center = true, size = [19.0500000000, 19.0500000000, 4.1110000000]);
														}
													}
												}
											}
										}
										translate(v = [85.7250000000, 0, 0]) {
											translate(v = [0, -57.1500000000, 0]) {
												translate(v = [9.5250000000, 0, 0]) {
													translate(v = [0, -9.5250000000, 0]) {
														translate(v = [0, 0, -1.5000000000]) {
															cube(center = true, size = [19.0500000000, 19.0500000000, 4.1110000000]);
														}
													}
												}
											}
										}
										translate(v = [85.7250000000, 0, 0]) {
											translate(v = [0, -0.0000000000, 0]) {
												translate(v = [9.5250000000, 0, 0]) {
													translate(v = [0, -9.5250000000, 0]) {
														translate(v = [0, 0, -1.5000000000]) {
															cube(center = true, size = [19.0500000000, 19.0500000000, 4.1110000000]);
														}
													}
												}
											}
										}
									}
								}
							}
							union() {
								union() {
									translate(v = [0.0000000000, 0, 0]) {
										translate(v = [0, -76.2000000000, 0]) {
											union() {
												translate(v = [11.9062500000, 0, 0]) {
													translate(v = [0, -9.5250000000, 0]) {
														cube(center = true, size = [23.8125000000, 19.0500000000, 1.1110000000]);
													}
												}
												translate(v = [11.9062500000, 0, 0]) {
													translate(v = [0, -9.5250000000, 0]) {
														difference() {
															translate(v = [0, 0, -1.5000000000]) {
																cube(center = true, size = [23.8125000000, 19.0500000000, 4.1110000000]);
															}
															translate(v = [0, 0, -1.5000000000]) {
																cube(center = true, size = [22.3125000000, 17.5500000000, 6.0000000000]);
															}
														}
													}
												}
											}
										}
									}
									translate(v = [0.0000000000, 0, 0]) {
										translate(v = [0, -57.1500000000, 0]) {
											union() {
												translate(v = [14.2875000000, 0, 0]) {
													translate(v = [0, -9.5250000000, 0]) {
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
