Dholydai/writerz-with-an-attitude/Dhlyd2HandMaximus/Pcb2HndMax/Dhlyd2HndMax26.kicad_sch

## KiCad design Dhlyd2HandMaximus/Pcb2HndMax/Dhlyd2HndMax26.kicad_sch (2026-07-24)

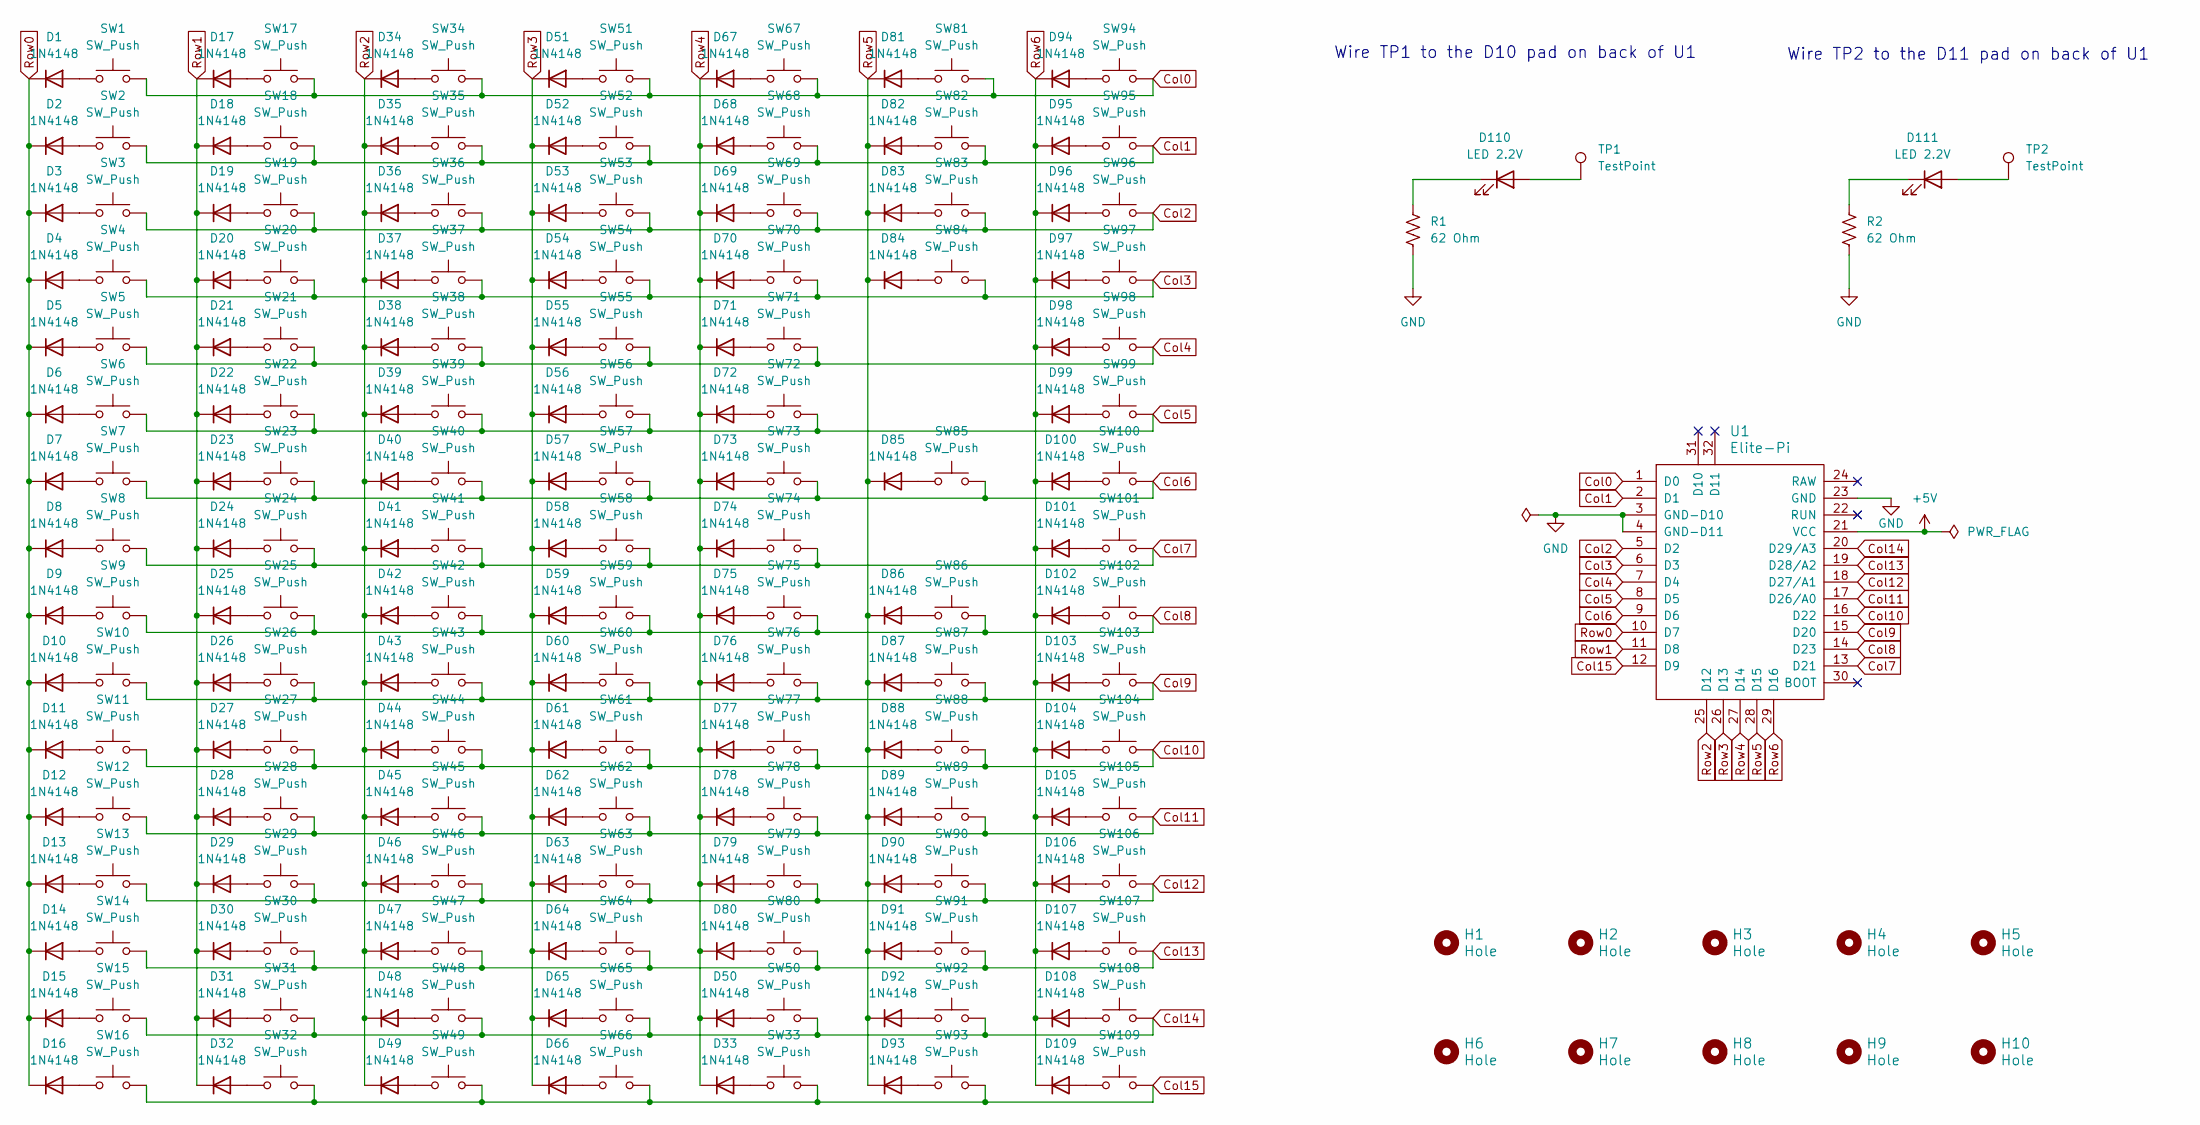
[picture p50: schematic Dhlyd2HndMax26.kicad_sch]

Parts:
D1, D2, D3, D4, D5, D6, D7, D8, D9, D10, D11, D12, D13, D14, D15, D16, D17, D18, D19, D20, D21, D22, D23, D24, D25, D26, D27, D28, D29, D30, D31, D32, D33, D34, D35, D36, D37, D38, D39, D40, D41, D42, D43, D44, D45, D46, D47, D48, D49, D50, D51, D52, D53, D54, D55, D56, D57, D58, D59, D60, D61, D62, D63, D64, D65, D66, D67, D68, D69, D70, D71, D72, D73, D74, D75, D76, D77, D78, D79, D80, D81, D82, D83, D84, D85, D86, D87, D88, D89, D90, D91, D92, D93, D94, D95, D96, D97, D98, D99, D100, D101, D102, D103, D104, D105, D106, D107, D108, D109: 1N4148; D_DO-35_SOD27_P7.62mm_Horizontal
D110, D111: LED 2.2V; SW_Ch_MX_LED_Template
H1, H2, H3, H4, H5, H6, H7, H8, H9, H10: Hole; MountingHole_3.2mm_M3_Pad
R1, R2: 62 Ohm; R_Axial_DIN0207_L6.3mm_D2.5mm_P10.16mm_Horizontal
SW1, SW2, SW3, SW4, SW5, SW6, SW7, SW8, SW9, SW10, SW11, SW12, SW13, SW14, SW15, SW16, SW18, SW19, SW20, SW21, SW22, SW23, SW24, SW25, SW26, SW27, SW28, SW29, SW31, SW32, SW33, SW35, SW36, SW37, SW38, SW39, SW40, SW41, SW42, SW43, SW44, SW45, SW46, SW48, SW49, SW50, SW52, SW53, SW54, SW55, SW56, SW58, SW59, SW60, SW61, SW62, SW64, SW65, SW66, SW68, SW69, SW70, SW71, SW72, SW74, SW75, SW76, SW77, SW78, SW80, SW82, SW83, SW87, SW88, SW90, SW91, SW92, SW94, SW95, SW96, SW97, SW98, SW99, SW100, SW102, SW103, SW104, SW105, SW106, SW107, SW109: SW_Push; SW_Cherry_MX_1.00u_PCB
SW17, SW30, SW67, SW79: SW_Push; SW_Cherry_MX_1.50u_PCB
SW34, SW47: SW_Push; SW_Cherry_MX_1.1666u_PCB
SW51, SW63: SW_Push; SW_Cherry_MX_1.8333u_PCB
SW57: SW_Push; SW_Cherry_MX_1.3333u_PCB
SW73, SW93: SW_Push; SW_Ch_Inv_MX_2.00u_PCB
SW81, SW84, SW86, SW89: SW_Push; SW_Cherry_MX_1.25u_PCB
SW85: SW_Push; SW_Ch_Inv_MX_6.00u_PCB_Stagger
SW101, SW108: SW_Push; SW_Ch_Inv_MX_2.00u_Vertical_PCB
TP1, TP2: TestPoint; TestPoint_Pad_D2.5mm
U1: Elite-Pi

Connections:
+5V: U1.21 (VCC)
Col0: SW1.2, SW17.2, SW34.2, SW51.2, SW67.2, SW81.2, SW94.2, U1.1 (D0)
Col1: SW2.2, SW18.2, SW35.2, SW52.2, SW68.2, SW82.2, SW95.2, U1.2 (D1)
Col2: SW3.2, SW19.2, SW36.2, SW53.2, SW69.2, SW83.2, SW96.2, U1.5 (D2)
Col3: SW4.2, SW20.2, SW37.2, SW54.2, SW70.2, SW84.2, SW97.2, U1.6 (D3)
Col4: SW5.2, SW21.2, SW38.2, SW55.2, SW71.2, SW98.2, U1.7 (D4)
Col5: SW6.2, SW22.2, SW39.2, SW56.2, SW72.2, SW99.2, U1.8 (D5)
Col6: SW7.2, SW23.2, SW40.2, SW57.2, SW73.2, SW85.2, SW100.2, U1.9 (D6)
Col7: SW8.2, SW24.2, SW41.2, SW58.2, SW74.2, SW101.2, U1.13 (D21)
Col8: SW9.2, SW25.2, SW42.2, SW59.2, SW75.2, SW86.2, SW102.2, U1.14 (D23)
Col9: SW10.2, SW26.2, SW43.2, SW60.2, SW76.2, SW87.2, SW103.2, U1.15 (D20)
Col10: SW11.2, SW27.2, SW44.2, SW61.2, SW77.2, SW88.2, SW104.2, U1.16 (D22)
Col11: SW12.2, SW28.2, SW45.2, SW62.2, SW78.2, SW89.2, SW105.2, U1.17 (D26/A0)
Col12: SW13.2, SW29.2, SW46.2, SW63.2, SW79.2, SW90.2, SW106.2, U1.18 (D27/A1)
Col13: SW14.2, SW30.2, SW47.2, SW64.2, SW80.2, SW91.2, SW107.2, U1.19 (D28/A2)
Col14: SW15.2, SW31.2, SW48.2, SW50.2, SW65.2, SW92.2, SW108.2, U1.20 (D29/A3)
Col15: SW16.2, SW32.2, SW33.2, SW49.2, SW66.2, SW93.2, SW109.2, U1.12 (D9)
GND: R1.2, R2.2, U1.3 (GND-D10), U1.4 (GND-D11), U1.23 (GND)
unnamed: D1.2 (A), SW1.1
unnamed: D2.2 (A), SW2.1
unnamed: D3.2 (A), SW3.1
unnamed: D4.2 (A), SW4.1
unnamed: D5.2 (A), SW5.1
unnamed: D6.2 (A), SW6.1
unnamed: D7.2 (A), SW7.1
unnamed: D8.2 (A), SW8.1
unnamed: D9.2 (A), SW9.1
unnamed: D10.2 (A), SW10.1
unnamed: D11.2 (A), SW11.1
unnamed: D12.2 (A), SW12.1
unnamed: D13.2 (A), SW13.1
unnamed: D14.2 (A), SW14.1
unnamed: D15.2 (A), SW15.1
unnamed: D16.2 (A), SW16.1
unnamed: D17.2 (A), SW17.1
unnamed: D18.2 (A), SW18.1
unnamed: D19.2 (A), SW19.1
unnamed: D20.2 (A), SW20.1
unnamed: D21.2 (A), SW21.1
unnamed: D22.2 (A), SW22.1
unnamed: D23.2 (A), SW23.1
unnamed: D24.2 (A), SW24.1
unnamed: D25.2 (A), SW25.1
unnamed: D26.2 (A), SW26.1
unnamed: D27.2 (A), SW27.1
unnamed: D28.2 (A), SW28.1
unnamed: D29.2 (A), SW29.1
unnamed: D30.2 (A), SW30.1
unnamed: D31.2 (A), SW31.1
unnamed: D32.2 (A), SW32.1
unnamed: D33.2 (A), SW33.1
unnamed: D34.2 (A), SW34.1
unnamed: D35.2 (A), SW35.1
unnamed: D36.2 (A), SW36.1
unnamed: D37.2 (A), SW37.1
unnamed: D38.2 (A), SW38.1
unnamed: D39.2 (A), SW39.1
unnamed: D40.2 (A), SW40.1
unnamed: D41.2 (A), SW41.1
unnamed: D42.2 (A), SW42.1
unnamed: D43.2 (A), SW43.1
unnamed: D44.2 (A), SW44.1
unnamed: D45.2 (A), SW45.1
unnamed: D46.2 (A), SW46.1
unnamed: D47.2 (A), SW47.1
unnamed: D48.2 (A), SW48.1
unnamed: D49.2 (A), SW49.1
unnamed: D50.2 (A), SW50.1
unnamed: D51.2 (A), SW51.1
unnamed: D52.2 (A), SW52.1
unnamed: D53.2 (A), SW53.1
unnamed: D54.2 (A), SW54.1
unnamed: D55.2 (A), SW55.1
unnamed: D56.2 (A), SW56.1
unnamed: D57.2 (A), SW57.1
unnamed: D58.2 (A), SW58.1
unnamed: D59.2 (A), SW59.1
unnamed: D60.2 (A), SW60.1
unnamed: D61.2 (A), SW61.1
unnamed: D62.2 (A), SW62.1
unnamed: D63.2 (A), SW63.1
unnamed: D64.2 (A), SW64.1
unnamed: D65.2 (A), SW65.1
unnamed: D66.2 (A), SW66.1
unnamed: D67.2 (A), SW67.1
unnamed: D68.2 (A), SW68.1
unnamed: D69.2 (A), SW69.1
unnamed: D70.2 (A), SW70.1
unnamed: D71.2 (A), SW71.1
unnamed: D72.2 (A), SW72.1
unnamed: D73.2 (A), SW73.1
unnamed: D74.2 (A), SW74.1
unnamed: D75.2 (A), SW75.1
unnamed: D76.2 (A), SW76.1
unnamed: D77.2 (A), SW77.1
unnamed: D78.2 (A), SW78.1
unnamed: D79.2 (A), SW79.1
unnamed: D80.2 (A), SW80.1
unnamed: D81.2 (A), SW81.1
unnamed: D82.2 (A), SW82.1
unnamed: D83.2 (A), SW83.1
unnamed: D84.2 (A), SW84.1
unnamed: D85.2 (A), SW85.1
unnamed: D86.2 (A), SW86.1
unnamed: D87.2 (A), SW87.1
unnamed: D88.2 (A), SW88.1
unnamed: D89.2 (A), SW89.1
unnamed: D90.2 (A), SW90.1
unnamed: D91.2 (A), SW91.1
unnamed: D92.2 (A), SW92.1
unnamed: D93.2 (A), SW93.1
unnamed: D94.2 (A), SW94.1
unnamed: D95.2 (A), SW95.1
unnamed: D96.2 (A), SW96.1
unnamed: D97.2 (A), SW97.1
unnamed: D98.2 (A), SW98.1
unnamed: D99.2 (A), SW99.1
unnamed: D100.2 (A), SW100.1
unnamed: D101.2 (A), SW101.1
unnamed: D102.2 (A), SW102.1
unnamed: D103.2 (A), SW103.1
unnamed: D104.2 (A), SW104.1
unnamed: D105.2 (A), SW105.1
unnamed: D106.2 (A), SW106.1
unnamed: D107.2 (A), SW107.1
unnamed: D108.2 (A), SW108.1
unnamed: D109.2 (A), SW109.1
unnamed: D110.1 (K), R1.1
unnamed: D110.2 (A), TP1.1
unnamed: D111.1 (K), R2.1
unnamed: D111.2 (A), TP2.1
Row0: D1.1 (K), D2.1 (K), D3.1 (K), D4.1 (K), D5.1 (K), D6.1 (K), D7.1 (K), D8.1 (K), D9.1 (K), D10.1 (K), D11.1 (K), D12.1 (K), D13.1 (K), D14.1 (K), D15.1 (K), D16.1 (K), U1.10 (D7)
Row1: D17.1 (K), D18.1 (K), D19.1 (K), D20.1 (K), D21.1 (K), D22.1 (K), D23.1 (K), D24.1 (K), D25.1 (K), D26.1 (K), D27.1 (K), D28.1 (K), D29.1 (K), D30.1 (K), D31.1 (K), D32.1 (K), U1.11 (D8)
Row2: D34.1 (K), D35.1 (K), D36.1 (K), D37.1 (K), D38.1 (K), D39.1 (K), D40.1 (K), D41.1 (K), D42.1 (K), D43.1 (K), D44.1 (K), D45.1 (K), D46.1 (K), D47.1 (K), D48.1 (K), D49.1 (K), U1.25 (D12)
Row3: D51.1 (K), D52.1 (K), D53.1 (K), D54.1 (K), D55.1 (K), D56.1 (K), D57.1 (K), D58.1 (K), D59.1 (K), D60.1 (K), D61.1 (K), D62.1 (K), D63.1 (K), D64.1 (K), D65.1 (K), D66.1 (K), U1.26 (D13)
Row4: D33.1 (K), D50.1 (K), D67.1 (K), D68.1 (K), D69.1 (K), D70.1 (K), D71.1 (K), D72.1 (K), D73.1 (K), D74.1 (K), D75.1 (K), D76.1 (K), D77.1 (K), D78.1 (K), D79.1 (K), D80.1 (K), U1.27 (D14)
Row5: D81.1 (K), D82.1 (K), D83.1 (K), D84.1 (K), D85.1 (K), D86.1 (K), D87.1 (K), D88.1 (K), D89.1 (K), D90.1 (K), D91.1 (K), D92.1 (K), D93.1 (K), U1.28 (D15)
Row6: D94.1 (K), D95.1 (K), D96.1 (K), D97.1 (K), D98.1 (K), D99.1 (K), D100.1 (K), D101.1 (K), D102.1 (K), D103.1 (K), D104.1 (K), D105.1 (K), D106.1 (K), D107.1 (K), D108.1 (K), D109.1 (K), U1.29 (D16)

Notes on the sheet:
Wire TP2 to the D11 pad on back of U1
Wire TP1 to the D10 pad on back of U1
